OLIMEX/DIY-LAPTOP/doc/web/hw_in-the-box.md

# What do you get in the package?

With your DIY kit, you will receive:

Description                          | Images
:-----------------------------------:|:-----------------------------------:
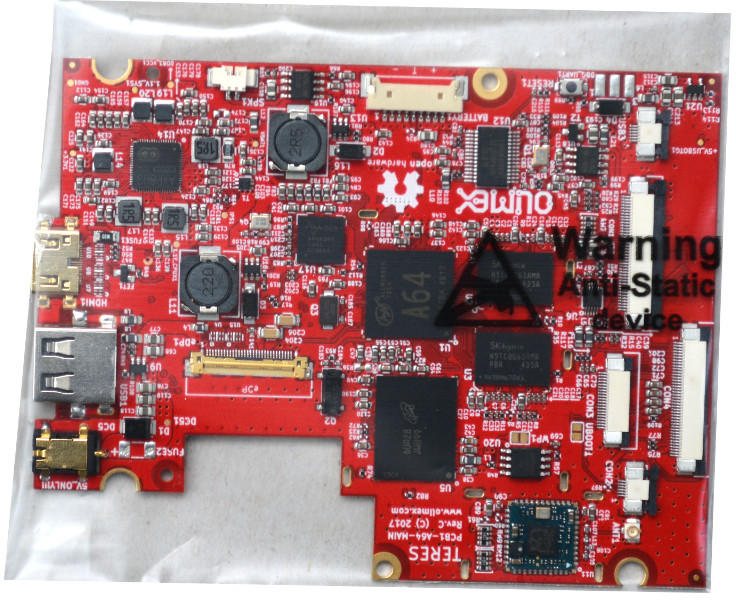
[picture p7: doc/images/TERES-I/hardware/001.jpg]
PCB1-A64-MAIN
| PCB1 (PCB1-A64-MAIN) – main PCB with A64 processor, 2GB RAM, 16GB eMMC. It is in an ESD protective bag. Please handle with proper anti-static precautions | 
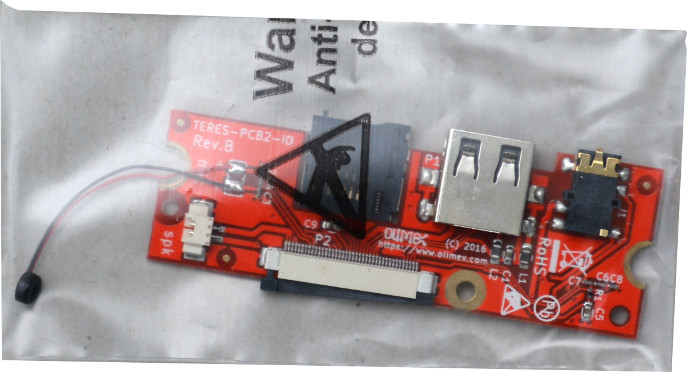
[picture p8: doc/images/TERES-I/hardware/002.jpg]
TERES-PCB2-IO
| PCB2 (TERES-PCB2-IO) – IO PCB with microphone, connectors for: speaker, USB, SD-card, headphones | 
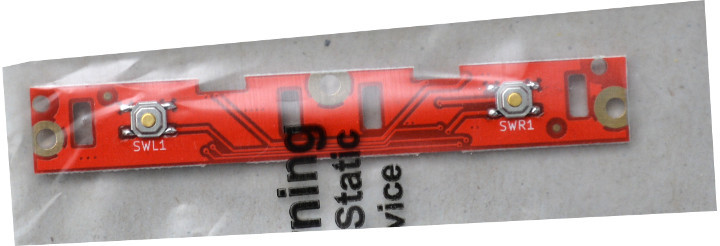
[picture p9: doc/images/TERES-I/hardware/003.jpg]
TERES-PCB3-TOUCH-BTN
| PCB3 (TERES-PCB3-TOUCH-BTN) – TOUCH two button PCB | 
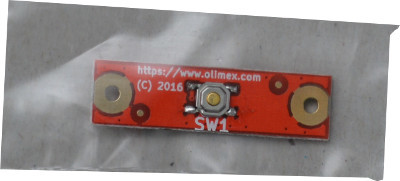
[picture p10: doc/images/TERES-I/hardware/004.jpg]
PCB4-PWR-BTN
| PCB4 – PWR PCB (PCB4-PWR-BTN) with button for power on/off | 
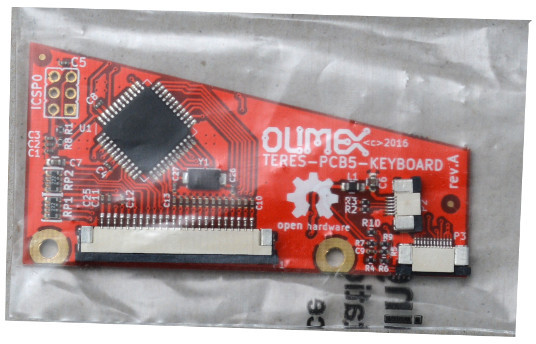
[picture p11: doc/images/TERES-I/hardware/005.jpg]
TERES-PCB5-KEYBOARD
| PCB5 (TERES-PCB5-KEYBOARD) – KEYBOARD PCB with controller of the keyboard and touchpad | 
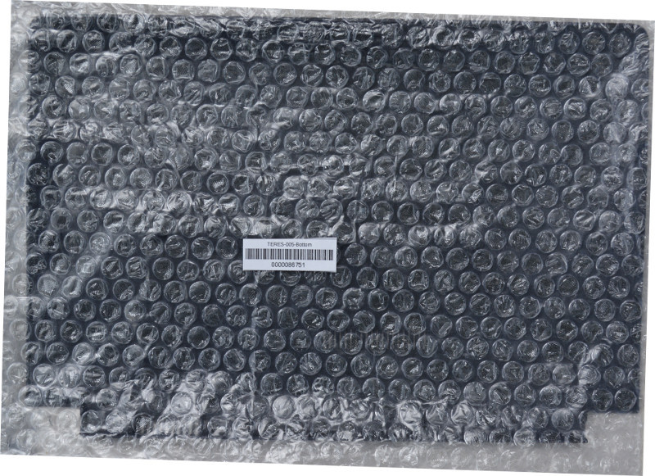
[picture p12: doc/images/TERES-I/hardware/006.jpg]
Bottom body 1
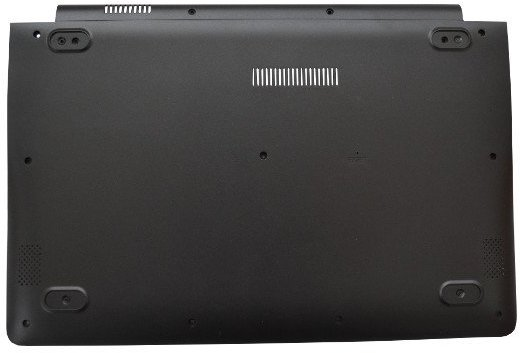
[picture p13: doc/images/TERES-I/hardware/007.jpg]
Bottom body 2
| Bottom body plastic part, packed in bubble wrap to protect from scratches |  
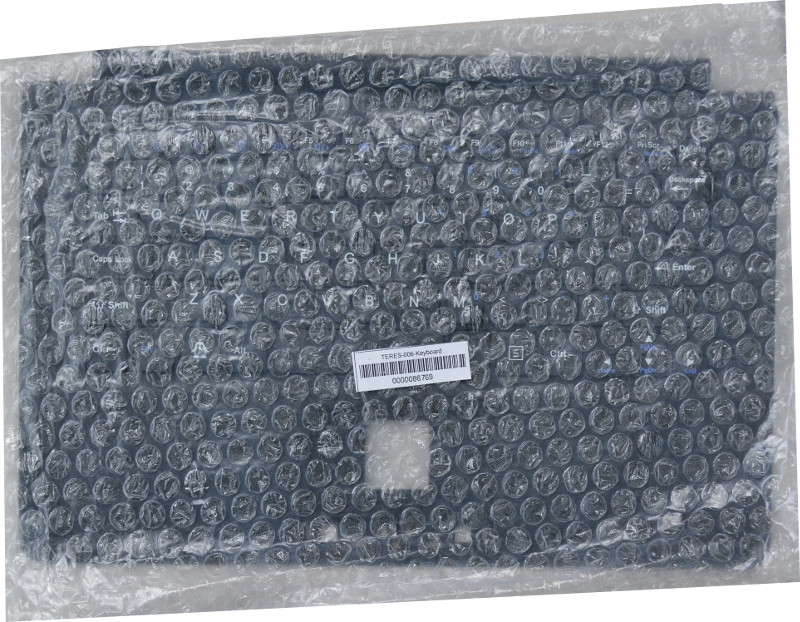
[picture p14: doc/images/TERES-I/hardware/008.jpg]
Keyboard body 1
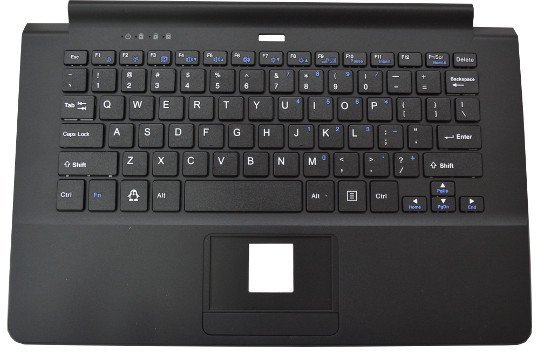
[picture p15: doc/images/TERES-I/hardware/009.jpg]
Keyboard body 2
| Keyboard body plastic assembly |  
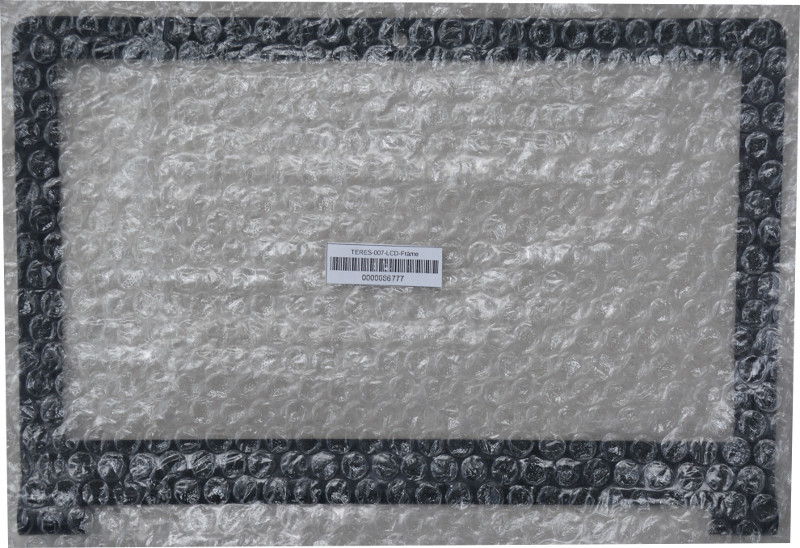
[picture p16: doc/images/TERES-I/hardware/010.jpg]
LCD frame 1
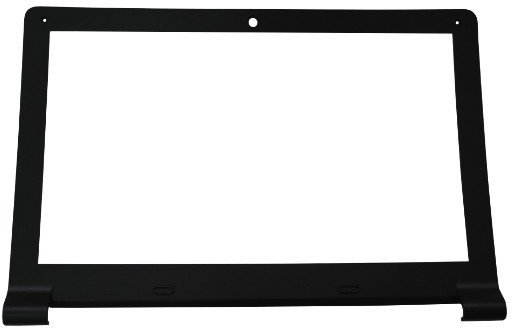
[picture p17: doc/images/TERES-I/hardware/011.jpg]
LCD frame 2
| LCD plastic frame |  
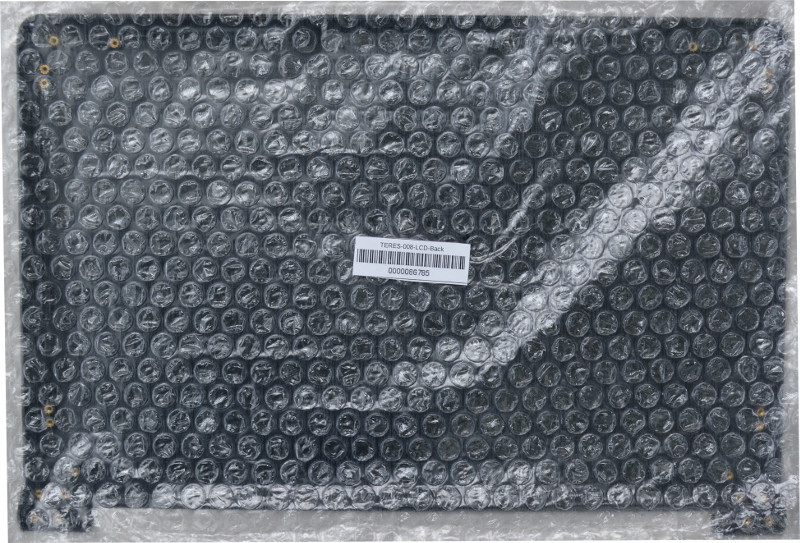
[picture p18: doc/images/TERES-I/hardware/012.jpg]
LCD body 1
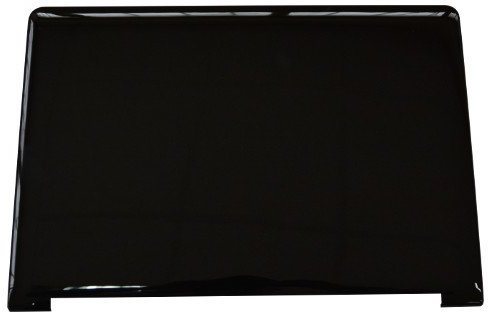
[picture p19: doc/images/TERES-I/hardware/013.jpg]
LCD body 2
| LCD back plastic body |  
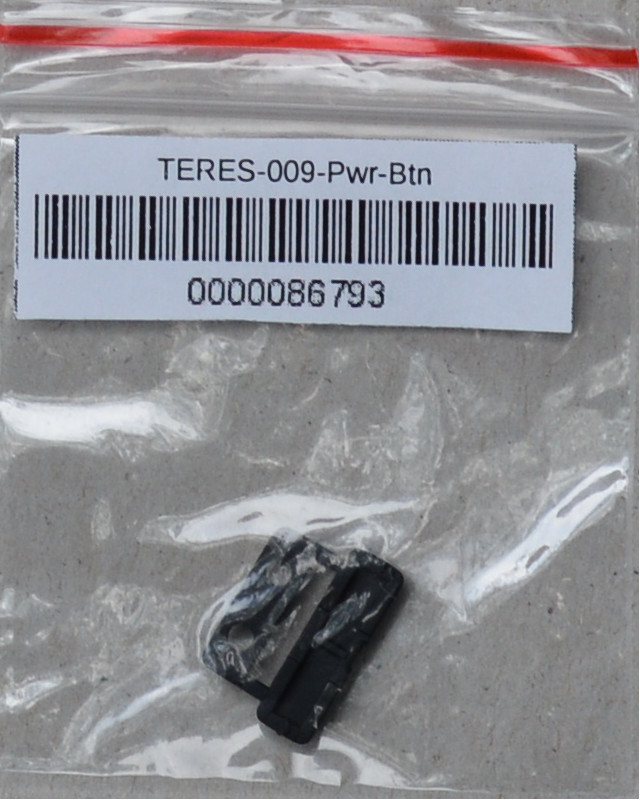
[picture p20: doc/images/TERES-I/hardware/014.jpg]
Power button 1
| Plastic power button |  Power button 2
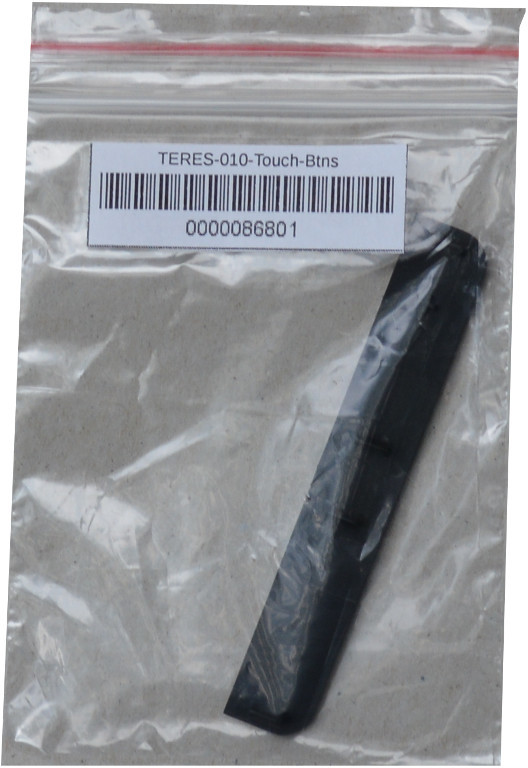
[picture p21: doc/images/TERES-I/hardware/016.jpg]
Touch button 1
| Plastic touch buttons |  Touch button 2
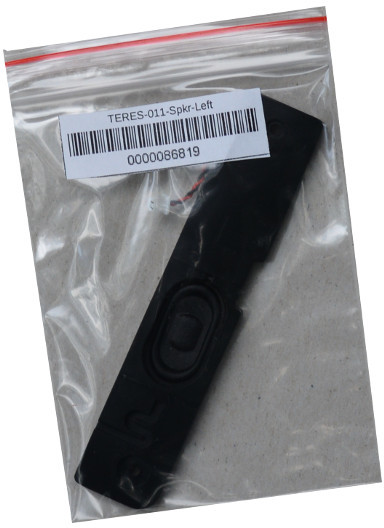
[picture p22: doc/images/TERES-I/hardware/018.jpg]
Left speaker 1
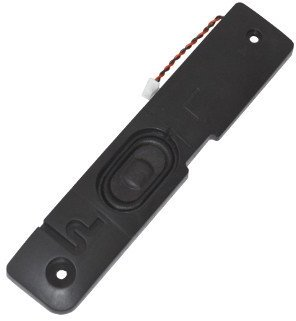
[picture p23: doc/images/TERES-I/hardware/019.jpg]
Left speaker 2
| Left speaker |  
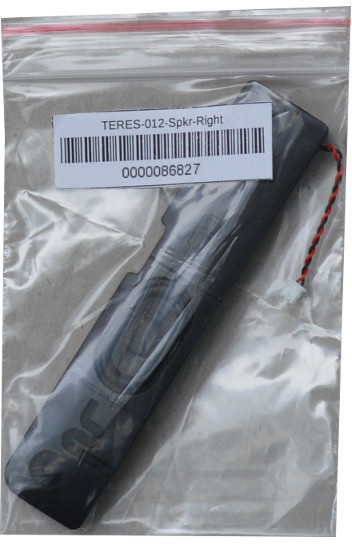
[picture p24: doc/images/TERES-I/hardware/020.jpg]
Right speaker 1
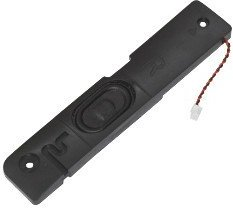
[picture p25: doc/images/TERES-I/hardware/021.jpg]
Right speaker 2
| Right speaker |  
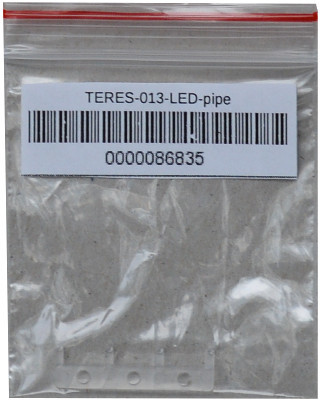
[picture p26: doc/images/TERES-I/hardware/022.jpg]
LED Pipe 1
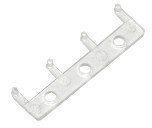
[picture p27: doc/images/TERES-I/hardware/023.jpg]
LED Pipe 2
| Transparent LED pipe |  
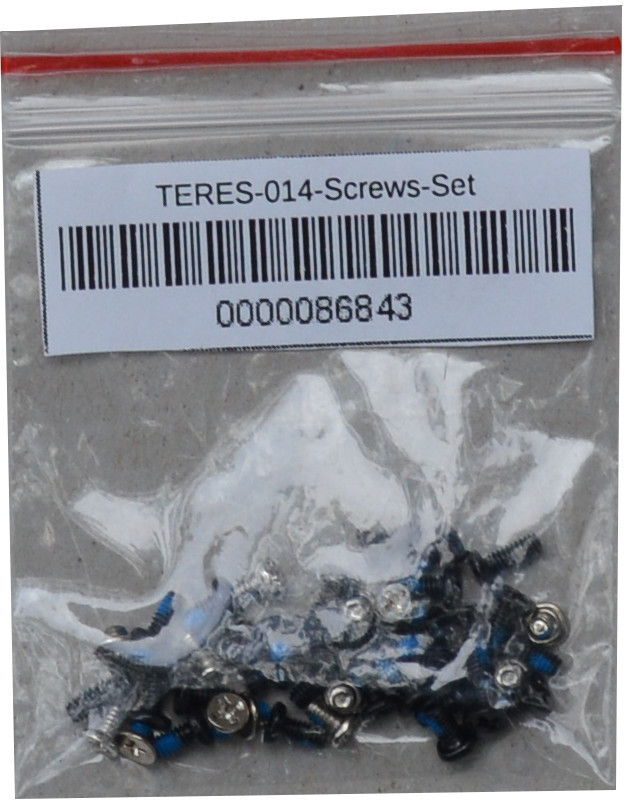
[picture p28: doc/images/TERES-I/hardware/024.jpg]
Screws 1
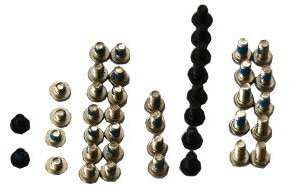
[picture p29: doc/images/TERES-I/hardware/025.jpg]
Screws 2
| Set of screws: M2x1.5 mm – 4 pcs; M2x3 mm – 9 pcs; M2x4 mm – 17 pcs; M2x5 mm – 12 pcs |  
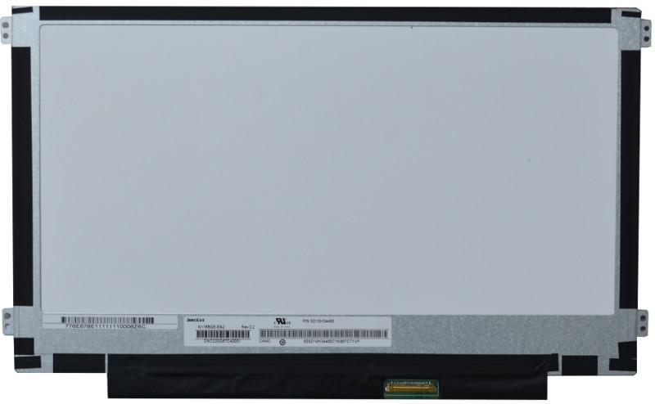
[picture p30: doc/images/TERES-I/hardware/026.jpg]
LCD 1
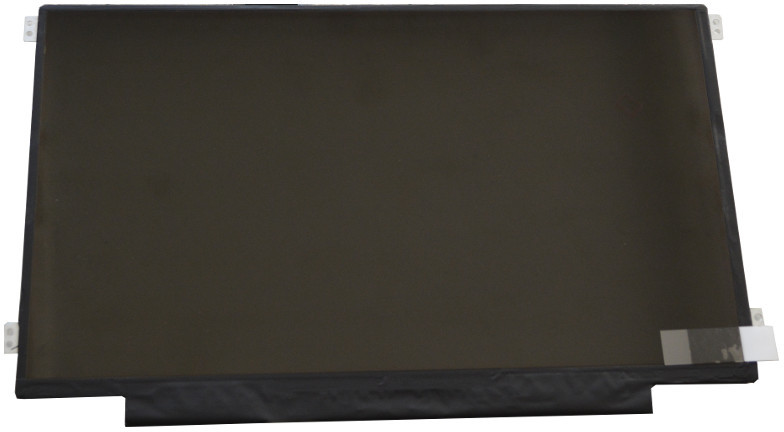
[picture p31: doc/images/TERES-I/hardware/027.jpg]
LCD 2
| [eDP](https://www.embedded.com/design/system-integration/4441940/eDP--A-better-embedded-display-ecosystem) 11.6" HD (1366x768) LCD. It has protective foil on top. [Datasheet](../datasheets/TERES-015-LCD11.6/N116BGE-EA2.pdf) |  
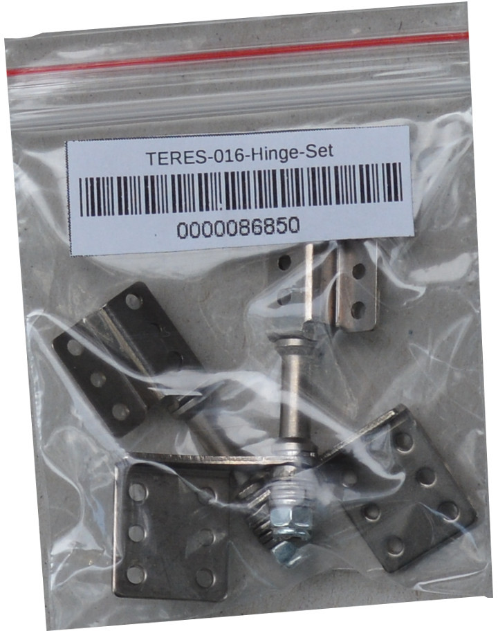
[picture p32: doc/images/TERES-I/hardware/028.jpg]
Hinges 1
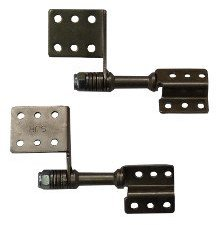
[picture p33: doc/images/TERES-I/hardware/029.jpg]
Hinges 2
| Left and right hinges |  
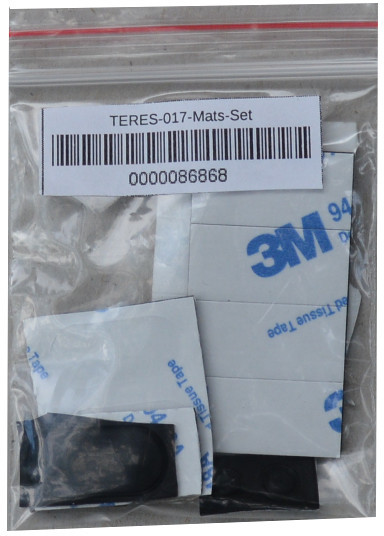
[picture p34: doc/images/TERES-I/hardware/030.jpg]
Mat 1
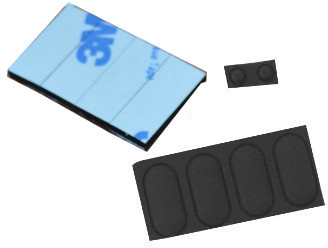
[picture p35: doc/images/TERES-I/hardware/031.jpg]
Mat 2
| Mat set. There are four rubber pads for the bottom of the laptop, two circular pads for LCD frame screws cover and four self adhesive mats for holding the battery. |  
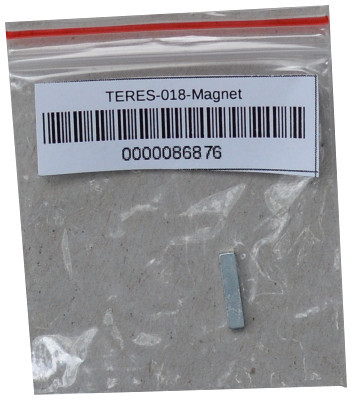
[picture p36: doc/images/TERES-I/hardware/032.jpg]
Magnet 1
| Magnet for the lid close sensor |  Magnet 2
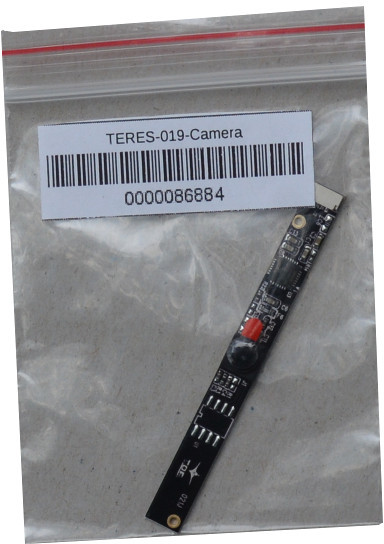
[picture p37: doc/images/TERES-I/hardware/034.jpg]
Camera 1
| Camera [[Datasheet](../../../HARDWARE/A64-TERES/TERES-019-Camera/N03A61B36DL32.pdf)] |  Camera 2
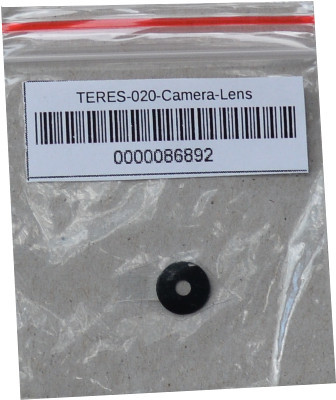
[picture p38: doc/images/TERES-I/hardware/036.jpg]
Camera lens 1
| Camera lens |  Camera lens 2
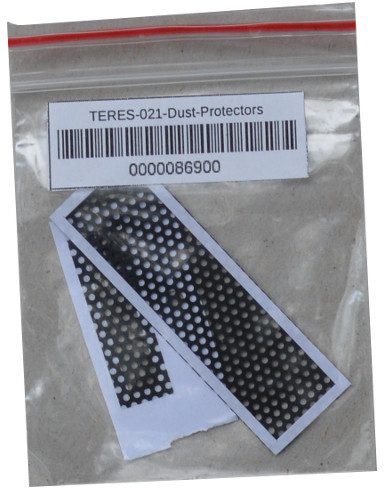
[picture p39: doc/images/TERES-I/hardware/038.jpg]
Dust protectors 1
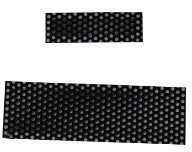
[picture p40: doc/images/TERES-I/hardware/039.jpg]
Dust protectors 2
| Two dust protectors – big and small |  
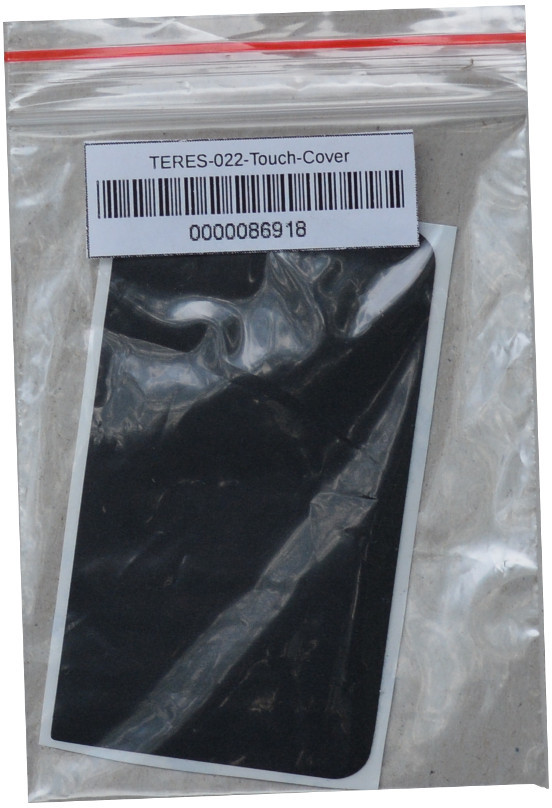
[picture p41: doc/images/TERES-I/hardware/040.jpg]
Touchpad cover 1
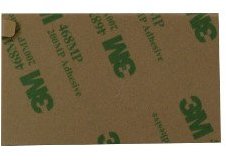
[picture p42: doc/images/TERES-I/hardware/042.jpg]
Touchpad cover 3
| Touchpad cover |  Touchpad cover 2 
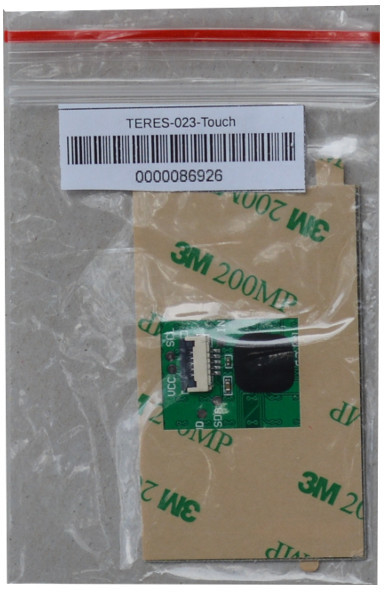
[picture p43: doc/images/TERES-I/hardware/043.jpg]
Touchpad
| Touchpad | 
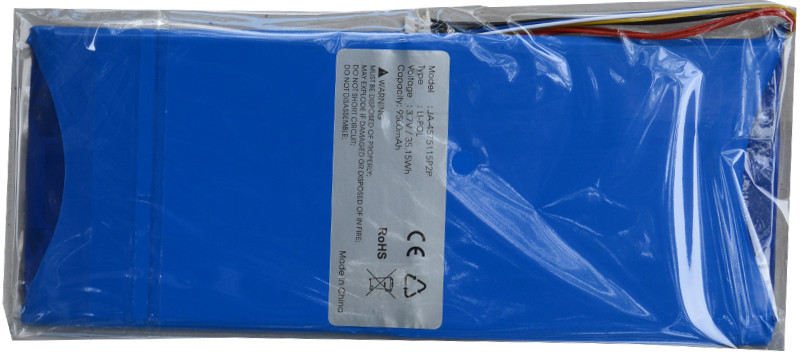
[picture p44: doc/images/TERES-I/hardware/044.jpg]
Battery
| LiPo battery 9500 mAh [[Datasheet](../../datasheets/LiPo-Battery/JA426992P2P-Spec-Data-Sheet-3.7V-7000mAh--161201.pdf)] | 
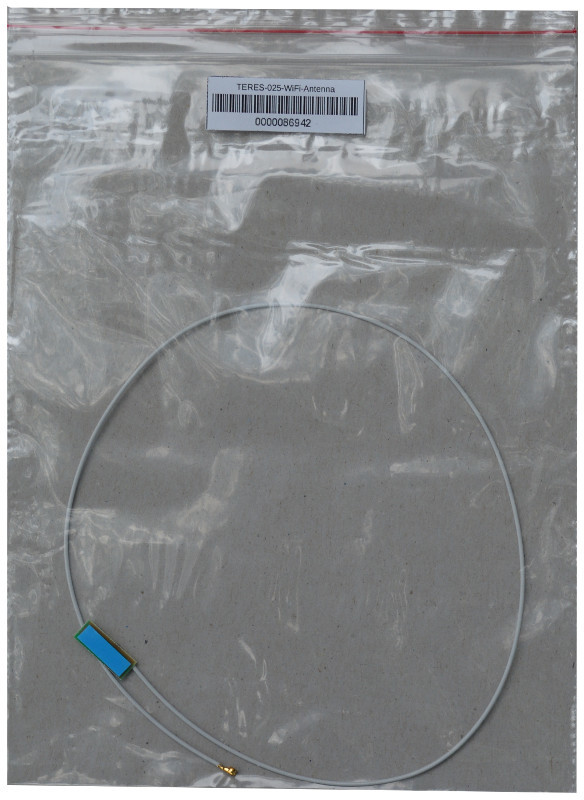
[picture p45: doc/images/TERES-I/hardware/045.jpg]
WiFi/Bluetooth 1
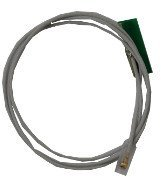
[picture p46: doc/images/TERES-I/hardware/046.jpg]
WiFi/Bluetooth 2
| WiFi/Bluetooth antenna |  
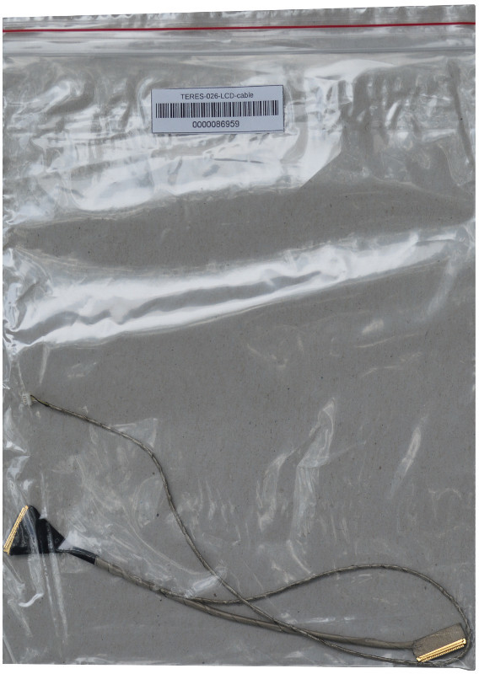
[picture p47: doc/images/TERES-I/hardware/047.jpg]
LCD/camera cable 1
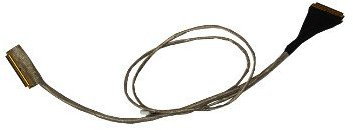
[picture p48: doc/images/TERES-I/hardware/048.jpg]
LCD/camera cable 2
| LCD/camera cable |  
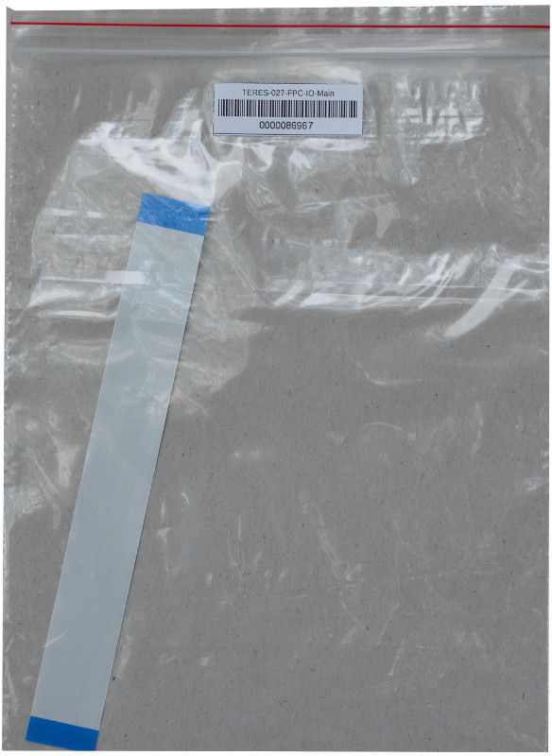
[picture p49: doc/images/TERES-I/hardware/049.jpg]
Main-IO cable 1
| Flat cable Main-IO |  Main-IO cable 2
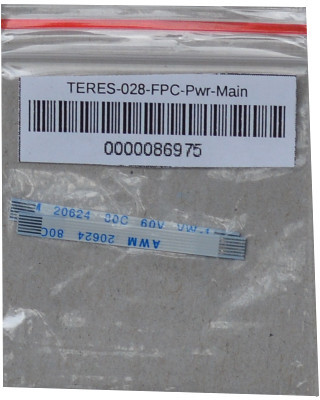
[picture p50: doc/images/TERES-I/hardware/051.jpg]
Flat cables 1
| Flat cable Power-Main, Flat cable Main-Keyboard |  Flat cables 2
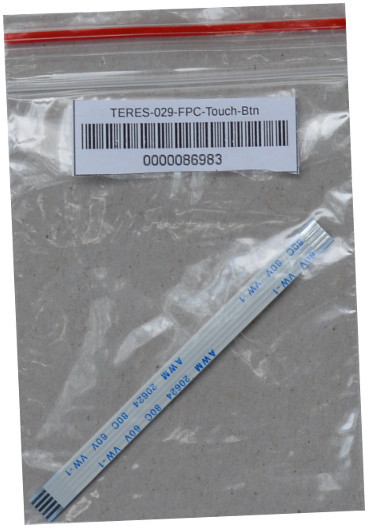
[picture p51: doc/images/TERES-I/hardware/053.jpg]
Touchpad-TouchButtons 1
| Flat cable Touchpad-TouchButtons |  Touchpad-TouchButtons 2
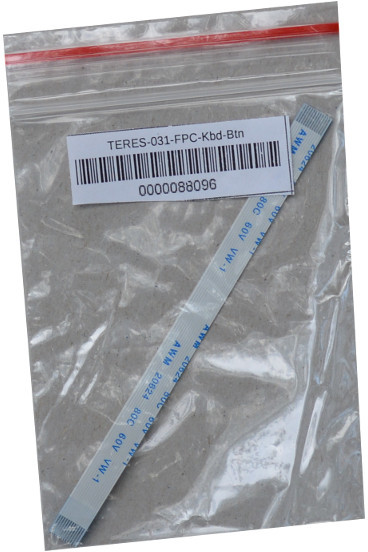
[picture p52: doc/images/TERES-I/hardware/055.jpg]
Keyboard-TouchButtons 1
| Flat cable Keyboard-TouchButtons |  Keyboard-TouchButtons 2
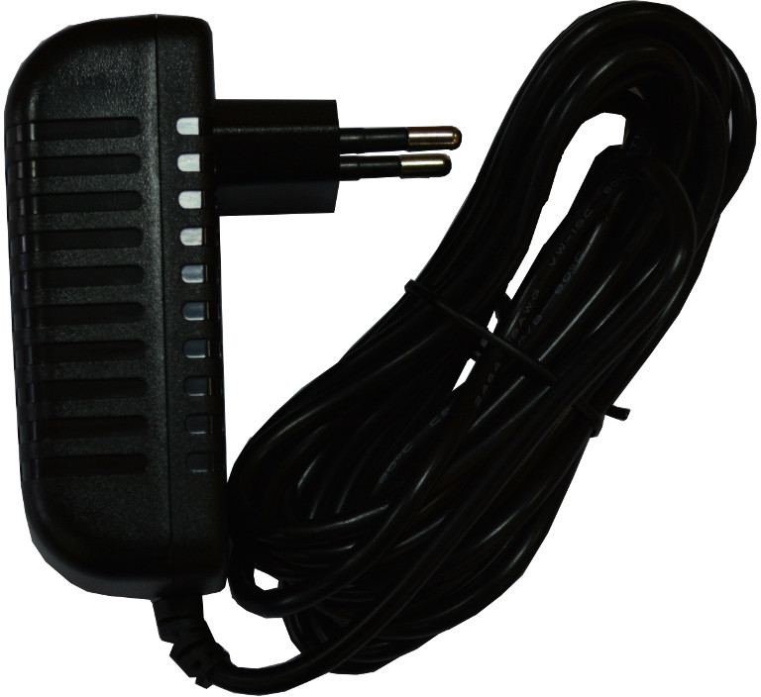
[picture p53: doc/images/TERES-I/hardware/057.jpg]
Power adapter 1
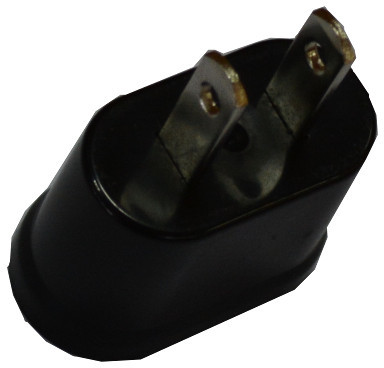
[picture p54: doc/images/TERES-I/hardware/058.jpg]
Power adapter 2
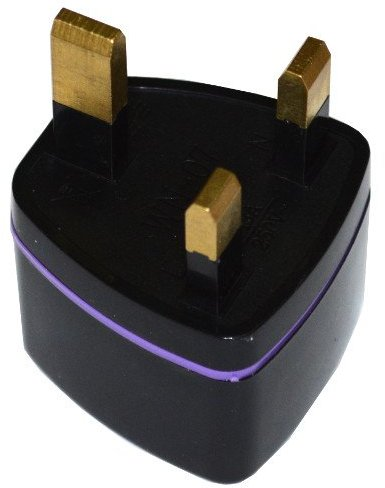
[picture p55: doc/images/TERES-I/hardware/059.jpg]
Power adapter 3
| Power adapter EU Style 5V 3A with 3 meter cable and LED status GREEN/RED indicator with UK and US plug adapters |
