OLIMEX/DIY-LAPTOP/index.rst

TERES-I User Manual
===================

.. toctree::
   :glob:
   :maxdepth: 2
   :caption: Overview

   doc/manuals/web/intro_what-is-teres-i
   doc/manuals/web/intro_name-origin
   doc/manuals/web/intro_what-is-unique
   doc/manuals/web/intro_importance-of-open-source
   doc/manuals/web/intro_sources

.. toctree::
   :glob:
   :maxdepth: 2
   :caption: Hardware

   doc/manuals/web/hw_intro
   doc/manuals/web/hw_in-the-box

.. toctree::
   :glob:
   :maxdepth: 2
   :caption: Assembling the TERES-I

   doc/manuals/web/hw_assembly

.. toctree::
   :glob:
   :maxdepth: 2
   :caption: Software

   doc/manuals/web/sw_fresh-os
   doc/manuals/web/sw_updating-os

.. toctree::
   :glob:
   :maxdepth: 2
   :caption: Resources

   doc/manuals/web/res_faq
   doc/manuals/web/res_troubleshooting
   doc/manuals/web/res_next-steps
   doc/manuals/web/res_community
