OLIMEX/DIY-LAPTOP/doc/web/res_community.md

# Community Links

<a href="https://www.github.com/OLIMEX" alt="GitHub" target="_blank" style="width: 50px; height: 50px" class="svg-link">
    <object data="../images/misc/icon-github.svg" type="image/svg+xml">
        
    </object>
</a>
<br>
<a href="https://twitter.com/Olimex" alt="Twitter" target="_blank" style="width: 50px; height: 50px" class="svg-link">
    <object data="../images/misc/icon-twitter.svg" type="image/svg+xml">
        
    </object>
</a>
<br>
<a href="https://olimex.wordpress.com" alt="Wordpress" target="_blank" style="width: 50px; height: 50px" class="svg-link">
    <object data="../images/misc/icon-wordpress.svg" type="image/svg+xml">
        
    </object>
</a>
<br>
<a href="https://www.facebook.com/OLINUXINO" alt="Facebook" target="_blank" style="width: 50px; height: 50px" class="svg-link">
    <object data="../images/misc/icon-facebook.svg" type="image/svg+xml">
        
    </object>
</a>
<br>
<a href="https://webchat.freenode.net/?channels=olimex" alt="IRC Web Chat" target="_blank" style="width: 50px; height: 50px" class="svg-link">
    <object data="../images/misc/icon-irc.jpg" type="image/svg+xml">
        
    </object>
</a>
