OLIMEX/DIY-LAPTOP/doc/images/TERES-I/TERES-A64-BLACK/laptop-3.jpg

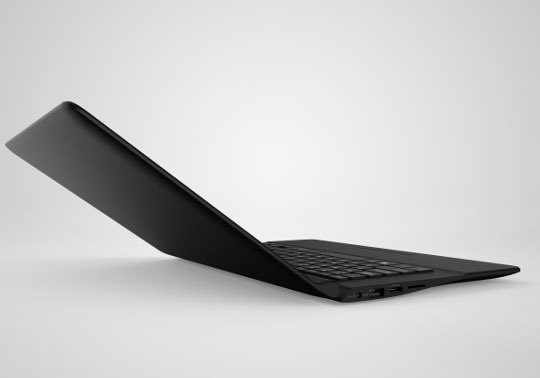
doc/images/TERES-I/TERES-A64-BLACK/laptop-3.jpg
