OLIMEX/DIY-LAPTOP/doc/images/TERES-I/TERES-A64-BLACK/laptop-9.jpg

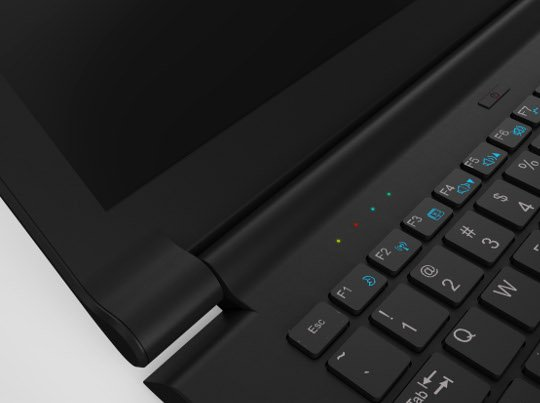
doc/images/TERES-I/TERES-A64-BLACK/laptop-9.jpg
