OLIMEX/DIY-LAPTOP/doc/images/TERES-I/TERES-A64-BLACK/laptop-16.jpg

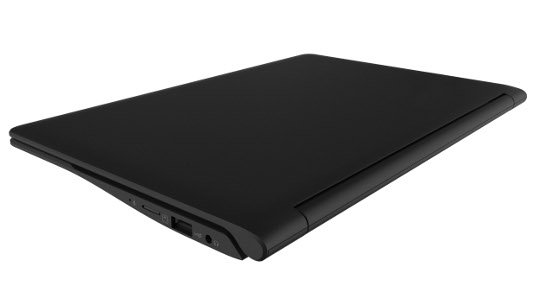
doc/images/TERES-I/TERES-A64-BLACK/laptop-16.jpg
