OLIMEX/DIY-LAPTOP/doc/images/TERES-I/TERES-A64-WHITE/laptop-1.jpg

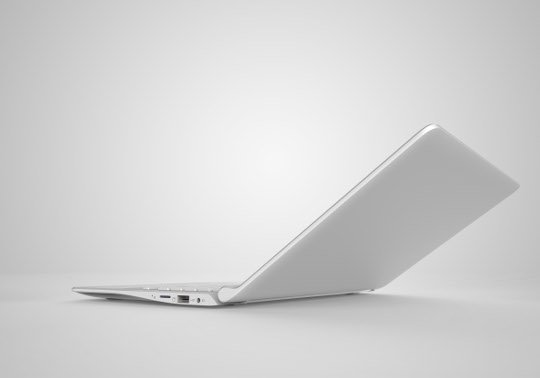
doc/images/TERES-I/TERES-A64-WHITE/laptop-1.jpg
