OLIMEX/DIY-LAPTOP/doc/images/TERES-I/TERES-A64-WHITE/laptop-5.jpg

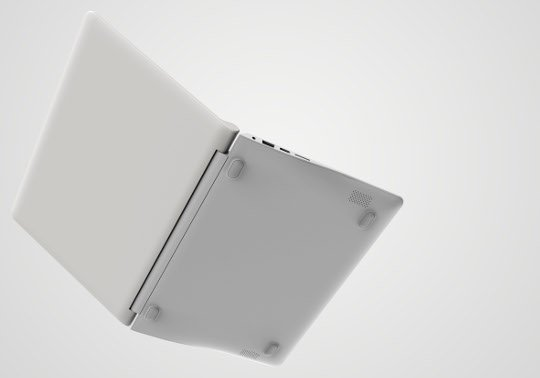
doc/images/TERES-I/TERES-A64-WHITE/laptop-5.jpg
