OLIMEX/DIY-LAPTOP/doc/images/TERES-I/TERES-A64-WHITE/laptop-7.jpg

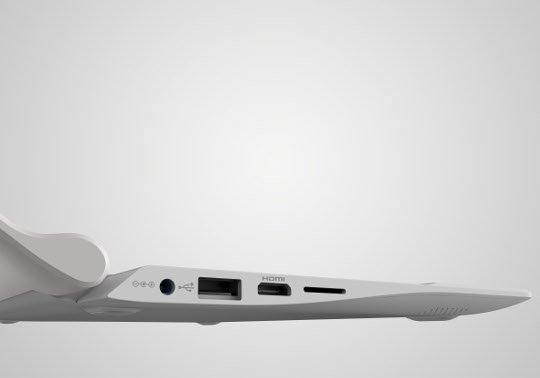
doc/images/TERES-I/TERES-A64-WHITE/laptop-7.jpg
