OLIMEX/DIY-LAPTOP/doc/images/TERES-I/TERES-A64-WHITE/laptop-15.jpg

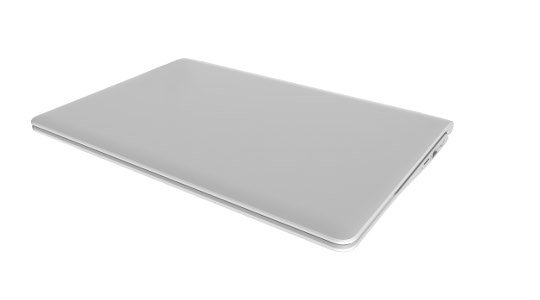
doc/images/TERES-I/TERES-A64-WHITE/laptop-15.jpg
