OLIMEX/DIY-LAPTOP/SOFTWARE/A64-TERES/blobs/bat/bat0.bmp

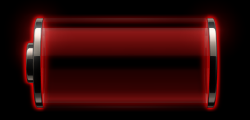
SOFTWARE/A64-TERES/blobs/bat/bat0.bmp
