OLIMEX/DIY-LAPTOP/SOFTWARE/A64-TERES/blobs/bat/bat1.bmp

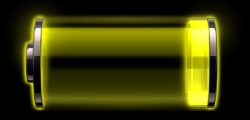
SOFTWARE/A64-TERES/blobs/bat/bat1.bmp
