OLIMEX/DIY-LAPTOP/SOFTWARE/A64-TERES/blobs/bat/bat2.bmp

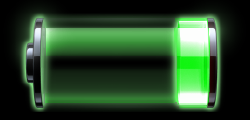
SOFTWARE/A64-TERES/blobs/bat/bat2.bmp
