OLIMEX/DIY-LAPTOP/SOFTWARE/A64-TERES/blobs/bat/bat3.bmp

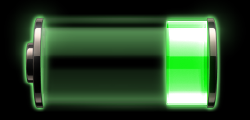
SOFTWARE/A64-TERES/blobs/bat/bat3.bmp
