OLIMEX/DIY-LAPTOP/SOFTWARE/A64-TERES/blobs/bat/bat4.bmp

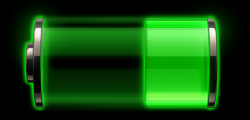
SOFTWARE/A64-TERES/blobs/bat/bat4.bmp
