OLIMEX/DIY-LAPTOP/SOFTWARE/A64-TERES/blobs/bat/bat5.bmp

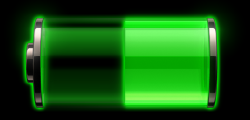
SOFTWARE/A64-TERES/blobs/bat/bat5.bmp
