OLIMEX/DIY-LAPTOP/SOFTWARE/A64-TERES/blobs/bat/bat6.bmp

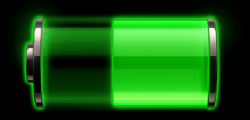
SOFTWARE/A64-TERES/blobs/bat/bat6.bmp
