OLIMEX/DIY-LAPTOP/SOFTWARE/A64-TERES/blobs/bat/bat7.bmp

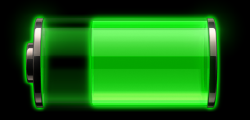
SOFTWARE/A64-TERES/blobs/bat/bat7.bmp
