OLIMEX/DIY-LAPTOP/SOFTWARE/A64-TERES/blobs/bat/bat8.bmp

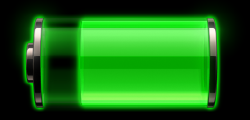
SOFTWARE/A64-TERES/blobs/bat/bat8.bmp
