OLIMEX/DIY-LAPTOP/SOFTWARE/A64-TERES/blobs/bat/bat9.bmp

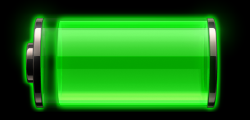
SOFTWARE/A64-TERES/blobs/bat/bat9.bmp
