OLIMEX/DIY-LAPTOP/SOFTWARE/A64-TERES/blobs/bat/bat10.bmp

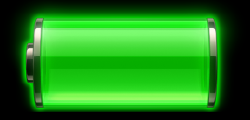
SOFTWARE/A64-TERES/blobs/bat/bat10.bmp
