OLIMEX/DIY-LAPTOP/SOFTWARE/A64-TERES/blobs/bat/battery.bmp

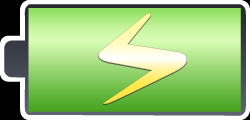
SOFTWARE/A64-TERES/blobs/bat/battery.bmp
