OLIMEX/DIY-LAPTOP/SOFTWARE/A64-TERES/blobs/bat/battery_charge.bmp

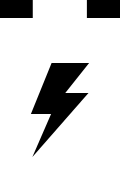
SOFTWARE/A64-TERES/blobs/bat/battery_charge.bmp
