OLIMEX/DIY-LAPTOP/SOFTWARE/A64-TERES/blobs/bat/bempty.bmp

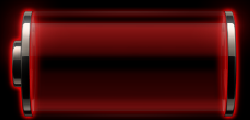
SOFTWARE/A64-TERES/blobs/bat/bempty.bmp
