OLIMEX/DIY-LAPTOP/SOFTWARE/A64-TERES/blobs/bat/low_pwr.bmp

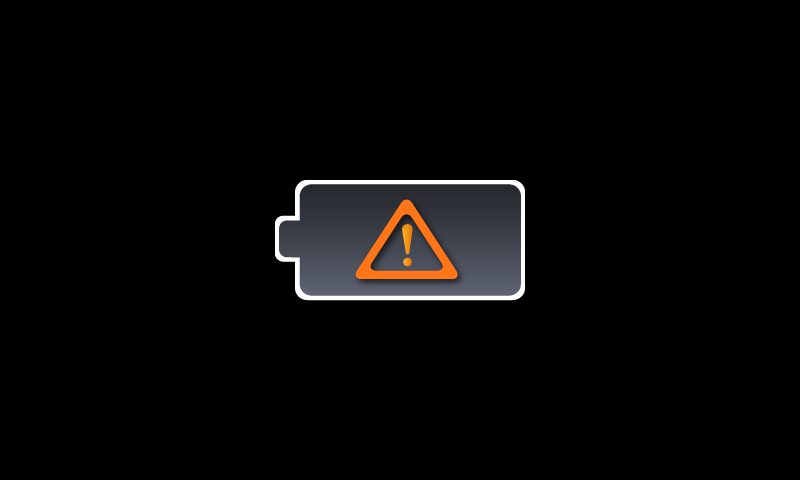
SOFTWARE/A64-TERES/blobs/bat/low_pwr.bmp
