OLIMEX/DIY-LAPTOP/HARDWARE/A64-TERES/TERES-PCB5-KEYBOARD/TERES-PCB5-KEYBOARD_Rev.A.ods

Designation | Quantity | Designator | Package
16.000MHz/SMD5x3.2/12pF | 1 | Y1 | Q5x3.25
ATMEGA16U4-A | 1 | U1 | TQFP44
FLEXCON-0.5-6 | 1 | P2 | FLEXCON-0.5-6
FLEXCON-0.5-12 | 1 | P3 | FLEXCON-0.5-12
FLEX-CONN-KBD-TERES-24x1 | 1 | P1 | FLEX-CONN-KBD-TERES-24x1
1uF | 1 | C1 | C0402
100nF | 6 | C2,C3,C4,C5,C8,C9 | C0402
1uF | 2 | C6,C7 | C_0603_5MIL_DWS
1nF | 16 | C10,C11,C12,C13,C14,C15,C16,C17,C18,C19,C20,C21,C22,C23,C24,C25 | C0402
20pF | 2 | C26,C27 | C0402
d.n.p.(HR2x3) | 1 | ICSP0 | HN2x3
FB0805 | 1 | L1 | L_0805_5MIL_DWS
d.n.p.(10K) | 1 | R1 | R_0402_5MIL_DWS
22R | 3 | R2,R3,R8 | R_0402_5MIL_DWS
10K | 6 | R4,R5,R6,R7,R9,R10 | R_0402_5MIL_DWS
4x1.5K_RA1206 | 2 | RP1,RP2 | R_MATRIX_4_KICAD
