OLIMEX/DIY-LAPTOP/SOFTWARE/A64-TERES/linux-a64/drivers/pinctrl/sunxi/pinctrl-sun8iw11p1.c

/*
 * Allwinner SoCs(sun8iw11p1) pinctrl driver.
 *
 * Copyright (C) 2014 Jackie Hwang
 *
 * Jackie Hwang <huangshr@allwinnertech.com>
 *
 * Copyright (C) 2014 Chen-Yu Tsai
 *
 * Chen-Yu Tsai <wens@csie.org>
 *
 * Copyright (C) 2014 Maxime Ripard
 *
 * Maxime Ripard <maxime.ripard@free-electrons.com>
 *
 * This file is licensed under the terms of the GNU General Public
 * License version 2.  This program is licensed "as is" without any
 * warranty of any kind, whether express or implied.
 */

#include <linux/module.h>
#include <linux/platform_device.h>
#include <linux/of.h>
#include <linux/of_device.h>
#include <linux/pinctrl/pinctrl.h>

#include "pinctrl-sunxi.h"
static const struct sunxi_desc_pin sun8iw11p1_pins[] = {
	SUNXI_PIN(SUNXI_PINCTRL_PIN(A, 0),
		  SUNXI_FUNCTION(0x0, "gpio_in"),
		  SUNXI_FUNCTION(0x1, "gpio_out"),
		  SUNXI_FUNCTION(0x2, "emac0"),		/* ERXD3 */
		  SUNXI_FUNCTION(0x3, "spi1"),		/* CS0 */
		  SUNXI_FUNCTION(0x4, "uart2"),		/* RTS */
		  SUNXI_FUNCTION(0x5, "gmac0"),		/* GRXD3 */
		  SUNXI_FUNCTION(0x7, "io_disabled")),
	SUNXI_PIN(SUNXI_PINCTRL_PIN(A, 1),
		  SUNXI_FUNCTION(0x0, "gpio_in"),
		  SUNXI_FUNCTION(0x1, "gpio_out"),
		  SUNXI_FUNCTION(0x2, "emac0"),		/* ERXD2 */
		  SUNXI_FUNCTION(0x3, "spi1"),		/* CLK */
		  SUNXI_FUNCTION(0x4, "uart2"),		/* CTS */
		  SUNXI_FUNCTION(0x5, "gmac0"),		/* GRXD2 */
		  SUNXI_FUNCTION(0x7, "io_disabled")),
	SUNXI_PIN(SUNXI_PINCTRL_PIN(A, 2),
		  SUNXI_FUNCTION(0x0, "gpio_in"),
		  SUNXI_FUNCTION(0x1, "gpio_out"),
		  SUNXI_FUNCTION(0x2, "emac0"),		/* ERXD1 */
		  SUNXI_FUNCTION(0x3, "spi1"),		/* MOSI */
		  SUNXI_FUNCTION(0x4, "uart2"),		/* TX */
		  SUNXI_FUNCTION(0x5, "gmac0"),		/* GRXD1 */
		  SUNXI_FUNCTION(0x7, "io_disabled")),
	SUNXI_PIN(SUNXI_PINCTRL_PIN(A, 3),
		  SUNXI_FUNCTION(0x0, "gpio_in"),
		  SUNXI_FUNCTION(0x1, "gpio_out"),
		  SUNXI_FUNCTION(0x2, "emac0"),		/* ERXD0 */
		  SUNXI_FUNCTION(0x3, "spi1"),		/* MISO */
		  SUNXI_FUNCTION(0x4, "uart2"),		/* RX */
		  SUNXI_FUNCTION(0x5, "gmac0"),		/* GRXD0 */
		  SUNXI_FUNCTION(0x7, "io_disabled")),
	SUNXI_PIN(SUNXI_PINCTRL_PIN(A, 4),
		  SUNXI_FUNCTION(0x0, "gpio_in"),
		  SUNXI_FUNCTION(0x1, "gpio_out"),
		  SUNXI_FUNCTION(0x2, "emac0"),		/* ETXD3 */
		  SUNXI_FUNCTION(0x3, "spi1"),		/* CS1 */
		  SUNXI_FUNCTION(0x5, "gmac0"),		/* GTXD3 */
		  SUNXI_FUNCTION(0x7, "io_disabled")),
	SUNXI_PIN(SUNXI_PINCTRL_PIN(A, 5),
		  SUNXI_FUNCTION(0x0, "gpio_in"),
		  SUNXI_FUNCTION(0x1, "gpio_out"),
		  SUNXI_FUNCTION(0x2, "emac0"),		/* ETXD2 */
		  SUNXI_FUNCTION(0x3, "spi3"),		/* CS0 */
		  SUNXI_FUNCTION(0x5, "gmac0"),		/* GTXD2 */
		  SUNXI_FUNCTION(0x7, "io_disabled")),
	SUNXI_PIN(SUNXI_PINCTRL_PIN(A, 6),
		  SUNXI_FUNCTION(0x0, "gpio_in"),
		  SUNXI_FUNCTION(0x1, "gpio_out"),
		  SUNXI_FUNCTION(0x2, "emac0"),		/* ETXD1 */
		  SUNXI_FUNCTION(0x3, "spi3"),		/* CLK */
		  SUNXI_FUNCTION(0x5, "gmac0"),		/* GTXD1 */
		  SUNXI_FUNCTION(0x7, "io_disabled")),
	SUNXI_PIN(SUNXI_PINCTRL_PIN(A, 7),
		  SUNXI_FUNCTION(0x0, "gpio_in"),
		  SUNXI_FUNCTION(0x1, "gpio_out"),
		  SUNXI_FUNCTION(0x2, "emac0"),		/* ETXD0 */
		  SUNXI_FUNCTION(0x3, "spi3"),		/* MOSI */
		  SUNXI_FUNCTION(0x5, "gmac0"),		/* GTXD0 */
		  SUNXI_FUNCTION(0x7, "io_disabled")),
	SUNXI_PIN(SUNXI_PINCTRL_PIN(A, 8),
		  SUNXI_FUNCTION(0x0, "gpio_in"),
		  SUNXI_FUNCTION(0x1, "gpio_out"),
		  SUNXI_FUNCTION(0x2, "emac0"),		/* ERXCK */
		  SUNXI_FUNCTION(0x3, "spi3"),		/* MISO */
		  SUNXI_FUNCTION(0x5, "gmac0"),		/* GRXCK */
		  SUNXI_FUNCTION(0x7, "io_disabled")),
	SUNXI_PIN(SUNXI_PINCTRL_PIN(A, 9),
		  SUNXI_FUNCTION(0x0, "gpio_in"),
		  SUNXI_FUNCTION(0x1, "gpio_out"),
		  SUNXI_FUNCTION(0x2, "emac0"),		/* ERXERR */
		  SUNXI_FUNCTION(0x3, "spi3"),		/* CS1 */
		  SUNXI_FUNCTION(0x5, "gmac0"),		/* GNULL / ERXERR */
		  SUNXI_FUNCTION(0x6, "i2s1"),		/* MCLK */
		  SUNXI_FUNCTION(0x7, "io_disabled")),
	SUNXI_PIN(SUNXI_PINCTRL_PIN(A, 10),
		  SUNXI_FUNCTION(0x0, "gpio_in"),
		  SUNXI_FUNCTION(0x1, "gpio_out"),
		  SUNXI_FUNCTION(0x2, "emac0"),		/* ERXDV */
		  SUNXI_FUNCTION(0x4, "uart1"),		/* TX */
		  SUNXI_FUNCTION(0x5, "gmac0"),		/* GRXCTL / ERXDV */
		  SUNXI_FUNCTION(0x7, "io_disabled")),
	SUNXI_PIN(SUNXI_PINCTRL_PIN(A, 11),
		  SUNXI_FUNCTION(0x0, "gpio_in"),
		  SUNXI_FUNCTION(0x1, "gpio_out"),
		  SUNXI_FUNCTION(0x2, "emac0"),		/* EMDC */
		  SUNXI_FUNCTION(0x4, "uart1"),		/* RX */
		  SUNXI_FUNCTION(0x5, "gmac0"),		/* GMDC */
		  SUNXI_FUNCTION(0x7, "io_disabled")),
	SUNXI_PIN(SUNXI_PINCTRL_PIN(A, 12),
		  SUNXI_FUNCTION(0x0, "gpio_in"),
		  SUNXI_FUNCTION(0x1, "gpio_out"),
		  SUNXI_FUNCTION(0x2, "emac0"),		/* EMDIO */
		  SUNXI_FUNCTION(0x3, "uart6"),		/* TX */
		  SUNXI_FUNCTION(0x4, "uart1"),		/* RTS */
		  SUNXI_FUNCTION(0x5, "gmac0"),		/* GMDIO */
		  SUNXI_FUNCTION(0x7, "io_disabled")),
	SUNXI_PIN(SUNXI_PINCTRL_PIN(A, 13),
		  SUNXI_FUNCTION(0x0, "gpio_in"),
		  SUNXI_FUNCTION(0x1, "gpio_out"),
		  SUNXI_FUNCTION(0x2, "emac0"),		/* ETXEN */
		  SUNXI_FUNCTION(0x3, "uart6"),		/* RX */
		  SUNXI_FUNCTION(0x4, "uart1"),		/* CTS */
		  SUNXI_FUNCTION(0x5, "gmac0"),		/* GTXCTL / ETXEN */
		  SUNXI_FUNCTION(0x7, "io_disabled")),
	SUNXI_PIN(SUNXI_PINCTRL_PIN(A, 14),
		  SUNXI_FUNCTION(0x0, "gpio_in"),
		  SUNXI_FUNCTION(0x1, "gpio_out"),
		  SUNXI_FUNCTION(0x2, "emac0"),		/* ETXCK */
		  SUNXI_FUNCTION(0x3, "uart7"),		/* TX */
		  SUNXI_FUNCTION(0x4, "uart1"),		/* DTR */
		  SUNXI_FUNCTION(0x5, "gmac0"),		/* GNULL / ETXCK */
		  SUNXI_FUNCTION(0x6, "i2s1"),		/* BCLK */
		  SUNXI_FUNCTION(0x7, "io_disabled")),
	SUNXI_PIN(SUNXI_PINCTRL_PIN(A, 15),
		  SUNXI_FUNCTION(0x0, "gpio_in"),
		  SUNXI_FUNCTION(0x1, "gpio_out"),
		  SUNXI_FUNCTION(0x2, "emac0"),		/* ECRS */
		  SUNXI_FUNCTION(0x3, "uart7"),		/* RX */
		  SUNXI_FUNCTION(0x4, "uart1"),		/* DSR */
		  SUNXI_FUNCTION(0x5, "gmac0"),		/* GTXCK / ECRS */
		  SUNXI_FUNCTION(0x6, "i2s1"),		/* LRCK */
		  SUNXI_FUNCTION(0x7, "io_disabled")),
	SUNXI_PIN(SUNXI_PINCTRL_PIN(A, 16),
		  SUNXI_FUNCTION(0x0, "gpio_in"),
		  SUNXI_FUNCTION(0x1, "gpio_out"),
		  SUNXI_FUNCTION(0x2, "emac0"),		/* ECOL */
		  SUNXI_FUNCTION(0x3, "can0"),		/* TX */
		  SUNXI_FUNCTION(0x4, "uart1"),		/* DCD */
		  SUNXI_FUNCTION(0x5, "gmac0"),		/* GCLKIN / ECOL */
		  SUNXI_FUNCTION(0x6, "i2s1"),		/* DO */
		  SUNXI_FUNCTION(0x7, "io_disabled")),
	SUNXI_PIN(SUNXI_PINCTRL_PIN(A, 17),
		  SUNXI_FUNCTION(0x0, "gpio_in"),
		  SUNXI_FUNCTION(0x1, "gpio_out"),
		  SUNXI_FUNCTION(0x2, "emac0"),		/* ETXERR */
		  SUNXI_FUNCTION(0x3, "can0"),		/* RX */
		  SUNXI_FUNCTION(0x4, "uart1"),		/* RING */
		  SUNXI_FUNCTION(0x5, "gmac0"),		/* GNULL / ETXERR */
		  SUNXI_FUNCTION(0x6, "i2s1"),		/* DI */
		  SUNXI_FUNCTION(0x7, "io_disabled")),

	/* Hole */
	SUNXI_PIN(SUNXI_PINCTRL_PIN(B, 0),
		  SUNXI_FUNCTION(0x0, "gpio_in"),
		  SUNXI_FUNCTION(0x1, "gpio_out"),
		  SUNXI_FUNCTION(0x2, "twi0"),		/* SCK */
		  SUNXI_FUNCTION(0x7, "io_disabled")),
	SUNXI_PIN(SUNXI_PINCTRL_PIN(B, 1),
		  SUNXI_FUNCTION(0x0, "gpio_in"),
		  SUNXI_FUNCTION(0x1, "gpio_out"),
		  SUNXI_FUNCTION(0x2, "twi0"),		/* SDA */
		  SUNXI_FUNCTION(0x7, "io_disabled")),
	SUNXI_PIN(SUNXI_PINCTRL_PIN(B, 2),
		  SUNXI_FUNCTION(0x0, "gpio_in"),
		  SUNXI_FUNCTION(0x1, "gpio_out"),
		  SUNXI_FUNCTION(0x2, "pwm0"),		/* PWM0 */
		  SUNXI_FUNCTION(0x7, "io_disabled")),
	SUNXI_PIN(SUNXI_PINCTRL_PIN(B, 3),
		  SUNXI_FUNCTION(0x0, "gpio_in"),
		  SUNXI_FUNCTION(0x1, "gpio_out"),
		  SUNXI_FUNCTION(0x2, "ir0"),		/* TX */
		  SUNXI_FUNCTION(0x4, "spdif0"),	/* MCLK */
		  SUNXI_FUNCTION(0x6, "stanbywfi"),	/* STANBYWFI */
		  SUNXI_FUNCTION(0x7, "io_disabled")),
	SUNXI_PIN(SUNXI_PINCTRL_PIN(B, 4),
		  SUNXI_FUNCTION(0x0, "gpio_in"),
		  SUNXI_FUNCTION(0x1, "gpio_out"),
		  SUNXI_FUNCTION(0x2, "ir0"),		/* RX */
		  SUNXI_FUNCTION(0x7, "io_disabled")),
	SUNXI_PIN(SUNXI_PINCTRL_PIN(B, 5),
		  SUNXI_FUNCTION(0x0, "gpio_in"),
		  SUNXI_FUNCTION(0x1, "gpio_out"),
		  SUNXI_FUNCTION(0x2, "i2s0"),		/* MCLK */
		  SUNXI_FUNCTION(0x3, "ac97"),		/* MCLK */
		  SUNXI_FUNCTION(0x7, "io_disabled")),
	SUNXI_PIN(SUNXI_PINCTRL_PIN(B, 6),
		  SUNXI_FUNCTION(0x0, "gpio_in"),
		  SUNXI_FUNCTION(0x1, "gpio_out"),
		  SUNXI_FUNCTION(0x2, "i2s0"),		/* BCLK */
		  SUNXI_FUNCTION(0x3, "ac97"),		/* BCLK */
		  SUNXI_FUNCTION(0x7, "io_disabled")),
	SUNXI_PIN(SUNXI_PINCTRL_PIN(B, 7),
		  SUNXI_FUNCTION(0x0, "gpio_in"),
		  SUNXI_FUNCTION(0x1, "gpio_out"),
		  SUNXI_FUNCTION(0x2, "i2s0"),		/* LRCK */
		  SUNXI_FUNCTION(0x3, "ac97"),		/* SYNC */
		  SUNXI_FUNCTION(0x7, "io_disabled")),
	SUNXI_PIN(SUNXI_PINCTRL_PIN(B, 8),
		  SUNXI_FUNCTION(0x0, "gpio_in"),
		  SUNXI_FUNCTION(0x1, "gpio_out"),
		  SUNXI_FUNCTION(0x2, "i2s0"),		/* DO0 */
		  SUNXI_FUNCTION(0x3, "ac97"),		/* DO */
		  SUNXI_FUNCTION(0x7, "io_disabled")),
	SUNXI_PIN(SUNXI_PINCTRL_PIN(B, 9),
		  SUNXI_FUNCTION(0x0, "gpio_in"),
		  SUNXI_FUNCTION(0x1, "gpio_out"),
		  SUNXI_FUNCTION(0x2, "i2s0"),		/* DO1 */
		  SUNXI_FUNCTION(0x7, "io_disabled")),
	SUNXI_PIN(SUNXI_PINCTRL_PIN(B, 10),
		  SUNXI_FUNCTION(0x0, "gpio_in"),
		  SUNXI_FUNCTION(0x1, "gpio_out"),
		  SUNXI_FUNCTION(0x2, "i2s0"),		/* DO2 */
		  SUNXI_FUNCTION(0x7, "io_disabled")),
	SUNXI_PIN(SUNXI_PINCTRL_PIN(B, 11),
		  SUNXI_FUNCTION(0x0, "gpio_in"),
		  SUNXI_FUNCTION(0x1, "gpio_out"),
		  SUNXI_FUNCTION(0x2, "i2s0"),		/* DO3 */
		  SUNXI_FUNCTION(0x7, "io_disabled")),
	SUNXI_PIN(SUNXI_PINCTRL_PIN(B, 12),
		  SUNXI_FUNCTION(0x0, "gpio_in"),
		  SUNXI_FUNCTION(0x1, "gpio_out"),
		  SUNXI_FUNCTION(0x2, "i2s0"),		/* DI */
		  SUNXI_FUNCTION(0x3, "ac97"),		/* DI */
		  SUNXI_FUNCTION(0x4, "spdif0"),	/* DI */
		  SUNXI_FUNCTION(0x7, "io_disabled")),
	SUNXI_PIN(SUNXI_PINCTRL_PIN(B, 13),
		  SUNXI_FUNCTION(0x0, "gpio_in"),
		  SUNXI_FUNCTION(0x1, "gpio_out"),
		  SUNXI_FUNCTION(0x2, "spi2"),		/* CS1 */
		  SUNXI_FUNCTION(0x4, "spdif0"),	/* DO */
		  SUNXI_FUNCTION(0x7, "io_disabled")),
	SUNXI_PIN(SUNXI_PINCTRL_PIN(B, 14),
		  SUNXI_FUNCTION(0x0, "gpio_in"),
		  SUNXI_FUNCTION(0x1, "gpio_out"),
		  SUNXI_FUNCTION(0x2, "spi2"),		/* CS0 */
		  SUNXI_FUNCTION(0x3, "jtag0"),		/* MS0 */
		  SUNXI_FUNCTION(0x7, "io_disabled")),
	SUNXI_PIN(SUNXI_PINCTRL_PIN(B, 15),
		  SUNXI_FUNCTION(0x0, "gpio_in"),
		  SUNXI_FUNCTION(0x1, "gpio_out"),
		  SUNXI_FUNCTION(0x2, "spi2"),		/* CLK */
		  SUNXI_FUNCTION(0x3, "jtag0"),		/* CK0 */
		  SUNXI_FUNCTION(0x7, "io_disabled")),
	SUNXI_PIN(SUNXI_PINCTRL_PIN(B, 16),
		  SUNXI_FUNCTION(0x0, "gpio_in"),
		  SUNXI_FUNCTION(0x1, "gpio_out"),
		  SUNXI_FUNCTION(0x2, "spi2"),		/* MOSI */
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
		  SUNXI_FUNCTION(0x0, "gpio_in"),
		  SUNXI_FUNCTION(0x1, "gpio_out"),
		  SUNXI_FUNCTION(0x2, "ts0"),		/* D4 */
		  SUNXI_FUNCTION(0x3, "csi0"),		/* D4 */
		  SUNXI_FUNCTION(0x7, "io_disabled")),
	SUNXI_PIN(SUNXI_PINCTRL_PIN(E, 9),
		  SUNXI_FUNCTION(0x0, "gpio_in"),
		  SUNXI_FUNCTION(0x1, "gpio_out"),
		  SUNXI_FUNCTION(0x2, "ts0"),		/* D5 */
		  SUNXI_FUNCTION(0x3, "csi0"),		/* D5 */
		  SUNXI_FUNCTION(0x7, "io_disabled")),
	SUNXI_PIN(SUNXI_PINCTRL_PIN(E, 10),
		  SUNXI_FUNCTION(0x0, "gpio_in"),
		  SUNXI_FUNCTION(0x1, "gpio_out"),
		  SUNXI_FUNCTION(0x2, "ts0"),		/* D6 */
		  SUNXI_FUNCTION(0x3, "csi0"),		/* D6 */
		  SUNXI_FUNCTION(0x7, "io_disabled")),
	SUNXI_PIN(SUNXI_PINCTRL_PIN(E, 11),
		  SUNXI_FUNCTION(0x0, "gpio_in"),
		  SUNXI_FUNCTION(0x1, "gpio_out"),
		  SUNXI_FUNCTION(0x2, "ts0"),		/* D7 */
		  SUNXI_FUNCTION(0x3, "csi0"),		/* D7 */
		  SUNXI_FUNCTION(0x7, "io_disabled")),

	/* Hole */
	SUNXI_PIN(SUNXI_PINCTRL_PIN(F, 0),
		  SUNXI_FUNCTION(0x0, "gpio_in"),
		  SUNXI_FUNCTION(0x1, "gpio_out"),
		  SUNXI_FUNCTION(0x2, "sdc0"),		/* D1 */
		  SUNXI_FUNCTION(0x4, "jtag0"),		/* MSI */
		  SUNXI_FUNCTION(0x7, "io_disabled")),
	SUNXI_PIN(SUNXI_PINCTRL_PIN(F, 1),
		  SUNXI_FUNCTION(0x0, "gpio_in"),
		  SUNXI_FUNCTION(0x1, "gpio_out"),
		  SUNXI_FUNCTION(0x2, "sdc0"),		/* D0 */
		  SUNXI_FUNCTION(0x4, "jtag0"),		/* DI1 */
		  SUNXI_FUNCTION(0x7, "io_disabled")),
	SUNXI_PIN(SUNXI_PINCTRL_PIN(F, 2),
		  SUNXI_FUNCTION(0x0, "gpio_in"),
		  SUNXI_FUNCTION(0x1, "gpio_out"),
		  SUNXI_FUNCTION(0x2, "sdc0"),		/* CLK */
		  SUNXI_FUNCTION(0x4, "uart0"),		/* TX */
		  SUNXI_FUNCTION(0x7, "io_disabled")),
	SUNXI_PIN(SUNXI_PINCTRL_PIN(F, 3),
		  SUNXI_FUNCTION(0x0, "gpio_in"),
		  SUNXI_FUNCTION(0x1, "gpio_out"),
		  SUNXI_FUNCTION(0x2, "sdc0"),		/* CMD */
		  SUNXI_FUNCTION(0x4, "jtag0"),		/* DO1 */
		  SUNXI_FUNCTION(0x7, "io_disabled")),
	SUNXI_PIN(SUNXI_PINCTRL_PIN(F, 4),
		  SUNXI_FUNCTION(0x0, "gpio_in"),
		  SUNXI_FUNCTION(0x1, "gpio_out"),
		  SUNXI_FUNCTION(0x2, "sdc0"),		/* D3 */
		  SUNXI_FUNCTION(0x4, "uart0"),		/* RX */
		  SUNXI_FUNCTION(0x7, "io_disabled")),
	SUNXI_PIN(SUNXI_PINCTRL_PIN(F, 5),
		  SUNXI_FUNCTION(0x0, "gpio_in"),
		  SUNXI_FUNCTION(0x1, "gpio_out"),
		  SUNXI_FUNCTION(0x2, "sdc0"),		/* D2 */
		  SUNXI_FUNCTION(0x4, "jtag0"),		/* CK1 */
		  SUNXI_FUNCTION(0x7, "io_disabled")),

	/* Hole */
	SUNXI_PIN(SUNXI_PINCTRL_PIN(G, 0),
		  SUNXI_FUNCTION(0x0, "gpio_in"),
		  SUNXI_FUNCTION(0x1, "gpio_out"),
		  SUNXI_FUNCTION(0x2, "ts1"),		/* CLK */
		  SUNXI_FUNCTION(0x3, "csi1"),		/* PCLK */
		  SUNXI_FUNCTION(0x4, "sdc1"),		/* CMD */
		  SUNXI_FUNCTION(0x7, "io_disabled")),
	SUNXI_PIN(SUNXI_PINCTRL_PIN(G, 1),
		  SUNXI_FUNCTION(0x0, "gpio_in"),
		  SUNXI_FUNCTION(0x1, "gpio_out"),
		  SUNXI_FUNCTION(0x2, "ts1"),		/* ERR */
		  SUNXI_FUNCTION(0x3, "csi1"),		/* MLCK */
		  SUNXI_FUNCTION(0x4, "sdc1"),		/* CLK */
		  SUNXI_FUNCTION(0x7, "io_disabled")),
	SUNXI_PIN(SUNXI_PINCTRL_PIN(G, 2),
		  SUNXI_FUNCTION(0x0, "gpio_in"),
		  SUNXI_FUNCTION(0x1, "gpio_out"),
		  SUNXI_FUNCTION(0x2, "ts1"),		/* SYNC */
		  SUNXI_FUNCTION(0x3, "csi1"),		/* HSYNC */
		  SUNXI_FUNCTION(0x4, "sdc1"),		/* D0 */
		  SUNXI_FUNCTION(0x7, "io_disabled")),
	SUNXI_PIN(SUNXI_PINCTRL_PIN(G, 3),
		  SUNXI_FUNCTION(0x0, "gpio_in"),
		  SUNXI_FUNCTION(0x1, "gpio_out"),
		  SUNXI_FUNCTION(0x2, "ts1"),		/* DVLD */
		  SUNXI_FUNCTION(0x3, "csi1"),		/* VSYNC */
		  SUNXI_FUNCTION(0x4, "sdc1"),		/* D1 */
		  SUNXI_FUNCTION(0x7, "io_disabled")),
	SUNXI_PIN(SUNXI_PINCTRL_PIN(G, 4),
		  SUNXI_FUNCTION(0x0, "gpio_in"),
		  SUNXI_FUNCTION(0x1, "gpio_out"),
		  SUNXI_FUNCTION(0x2, "ts1"),		/* D0 */
		  SUNXI_FUNCTION(0x3, "csi1"),		/* D0 */
		  SUNXI_FUNCTION(0x4, "sdc1"),		/* D2 */
		  SUNXI_FUNCTION(0x5, "csi0"),		/* D8 */
		  SUNXI_FUNCTION(0x7, "io_disabled")),
	SUNXI_PIN(SUNXI_PINCTRL_PIN(G, 5),
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
		  SUNXI_FUNCTION(0x0, "gpio_in"),
		  SUNXI_FUNCTION(0x1, "gpio_out"),
		  SUNXI_FUNCTION(0x2, "lcd1"),		/* D15 */
		  SUNXI_FUNCTION(0x3, "emac0"),		/* ETXD2 */
		  SUNXI_FUNCTION(0x4, "kp0"),		/* IN5 */
		  SUNXI_FUNCTION(0x5, "sim0"),		/* VPPPP */
		  SUNXI_FUNCTION(0x7, "csi1"),		/* D15 */
		  SUNXI_FUNCTION_IRQ_BANK(0x6, 0, 15)),
	SUNXI_PIN(SUNXI_PINCTRL_PIN(H, 16),
		  SUNXI_FUNCTION(0x0, "gpio_in"),
		  SUNXI_FUNCTION(0x1, "gpio_out"),
		  SUNXI_FUNCTION(0x2, "lcd1"),		/* D16 */
		  SUNXI_FUNCTION(0x3, "emac0"),		/* ETXD1 */
		  SUNXI_FUNCTION(0x4, "kp0"),		/* IN6 */
		  SUNXI_FUNCTION(0x7, "csi1"),		/* D16 */
		  SUNXI_FUNCTION_IRQ_BANK(0x6, 0, 16)),
	SUNXI_PIN(SUNXI_PINCTRL_PIN(H, 17),
		  SUNXI_FUNCTION(0x0, "gpio_in"),
		  SUNXI_FUNCTION(0x1, "gpio_out"),
		  SUNXI_FUNCTION(0x2, "lcd1"),		/* D17 */
		  SUNXI_FUNCTION(0x3, "emac0"),		/* ETXD0 */
		  SUNXI_FUNCTION(0x4, "kp0"),		/* IN7 */
		  SUNXI_FUNCTION(0x5, "sim0"),		/* VCCEN */
		  SUNXI_FUNCTION(0x7, "csi1"),		/* D17 */
		  SUNXI_FUNCTION_IRQ_BANK(0x6, 0, 17)),
	SUNXI_PIN(SUNXI_PINCTRL_PIN(H, 18),
		  SUNXI_FUNCTION(0x0, "gpio_in"),
		  SUNXI_FUNCTION(0x1, "gpio_out"),
		  SUNXI_FUNCTION(0x2, "lcd1"),		/* D18 */
		  SUNXI_FUNCTION(0x3, "emac0"),		/* ERXCK */
		  SUNXI_FUNCTION(0x4, "kp0"),		/* OUT0 */
		  SUNXI_FUNCTION(0x5, "sim0"),		/* SLK */
		  SUNXI_FUNCTION(0x7, "csi1"),		/* D18 */
		  SUNXI_FUNCTION_IRQ_BANK(0x6, 0, 18)),
	SUNXI_PIN(SUNXI_PINCTRL_PIN(H, 19),
		  SUNXI_FUNCTION(0x0, "gpio_in"),
		  SUNXI_FUNCTION(0x1, "gpio_out"),
		  SUNXI_FUNCTION(0x2, "lcd1"),		/* D19 */
		  SUNXI_FUNCTION(0x3, "emac0"),		/* ERXERR */
		  SUNXI_FUNCTION(0x4, "kp0"),		/* OUT1 */
		  SUNXI_FUNCTION(0x5, "sim0"),		/* SDA */
		  SUNXI_FUNCTION(0x7, "csi1"),		/* D19 */
		  SUNXI_FUNCTION_IRQ_BANK(0x6, 0, 19)),
	SUNXI_PIN(SUNXI_PINCTRL_PIN(H, 20),
		  SUNXI_FUNCTION(0x0, "gpio_in"),
		  SUNXI_FUNCTION(0x1, "gpio_out"),
		  SUNXI_FUNCTION(0x2, "lcd1"),		/* D20 */
		  SUNXI_FUNCTION(0x3, "emac0"),		/* ERXDV */
		  SUNXI_FUNCTION(0x4, "can0"),		/* TX */
		  SUNXI_FUNCTION(0x7, "csi1"),		/* D20 */
		  SUNXI_FUNCTION_IRQ_BANK(0x6, 0, 20)),
	SUNXI_PIN(SUNXI_PINCTRL_PIN(H, 21),
		  SUNXI_FUNCTION(0x0, "gpio_in"),
		  SUNXI_FUNCTION(0x1, "gpio_out"),
		  SUNXI_FUNCTION(0x2, "lcd1"),		/* D21 */
		  SUNXI_FUNCTION(0x3, "emac0"),		/* EMDC */
		  SUNXI_FUNCTION(0x4, "can1"),		/* RX */
		  SUNXI_FUNCTION(0x7, "csi1"),		/* D21 */
		  SUNXI_FUNCTION_IRQ_BANK(0x6, 0, 21)),
	SUNXI_PIN(SUNXI_PINCTRL_PIN(H, 22),
		  SUNXI_FUNCTION(0x0, "gpio_in"),
		  SUNXI_FUNCTION(0x1, "gpio_out"),
		  SUNXI_FUNCTION(0x2, "lcd1"),		/* D22 */
		  SUNXI_FUNCTION(0x3, "emac0"),		/* EMDIO */
		  SUNXI_FUNCTION(0x4, "kp0"),		/* OUT2 */
		  SUNXI_FUNCTION(0x5, "sdc1"),		/* CMD */
		  SUNXI_FUNCTION(0x7, "csi1")),		/* D22 */
	SUNXI_PIN(SUNXI_PINCTRL_PIN(H, 23),
		  SUNXI_FUNCTION(0x0, "gpio_in"),
		  SUNXI_FUNCTION(0x1, "gpio_out"),
		  SUNXI_FUNCTION(0x2, "lcd1"),		/* D23 */
		  SUNXI_FUNCTION(0x3, "emac0"),		/* ETXEN */
		  SUNXI_FUNCTION(0x4, "kp0"),		/* OUT3 */
		  SUNXI_FUNCTION(0x5, "sdc1"),		/* CLK */
		  SUNXI_FUNCTION(0x7, "csi1")),		/* D23 */
	SUNXI_PIN(SUNXI_PINCTRL_PIN(H, 24),
		  SUNXI_FUNCTION(0x0, "gpio_in"),
		  SUNXI_FUNCTION(0x1, "gpio_out"),
		  SUNXI_FUNCTION(0x2, "lcd1"),		/* CLK */
		  SUNXI_FUNCTION(0x3, "emac0"),		/* ETXCK */
		  SUNXI_FUNCTION(0x4, "kp0"),		/* OUT4 */
		  SUNXI_FUNCTION(0x5, "sdc1"),		/* D0 */
		  SUNXI_FUNCTION(0x7, "csi1")),		/* PCLK */
	SUNXI_PIN(SUNXI_PINCTRL_PIN(H, 25),
		  SUNXI_FUNCTION(0x0, "gpio_in"),
		  SUNXI_FUNCTION(0x1, "gpio_out"),
		  SUNXI_FUNCTION(0x2, "lcd1"),		/* DE */
		  SUNXI_FUNCTION(0x3, "emac0"),		/* ECRS */
		  SUNXI_FUNCTION(0x4, "kp0"),		/* OUT5 */
		  SUNXI_FUNCTION(0x5, "sdc1"),		/* D1 */
		  SUNXI_FUNCTION(0x7, "csi1")),		/* FIELD */
	SUNXI_PIN(SUNXI_PINCTRL_PIN(H, 26),
		  SUNXI_FUNCTION(0x0, "gpio_in"),
		  SUNXI_FUNCTION(0x1, "gpio_out"),
		  SUNXI_FUNCTION(0x2, "lcd1"),		/* HSYNC */
		  SUNXI_FUNCTION(0x3, "emac0"),		/* ECOL */
		  SUNXI_FUNCTION(0x4, "kp0"),		/* OUT6 */
		  SUNXI_FUNCTION(0x5, "sdc1"),		/* D2 */
		  SUNXI_FUNCTION(0x7, "csi1")),		/* HSYNC */
	SUNXI_PIN(SUNXI_PINCTRL_PIN(H, 27),
		  SUNXI_FUNCTION(0x0, "gpio_in"),
		  SUNXI_FUNCTION(0x1, "gpio_out"),
		  SUNXI_FUNCTION(0x2, "lcd1"),		/* VSYNC */
		  SUNXI_FUNCTION(0x3, "emac0"),		/* ETXERR */
		  SUNXI_FUNCTION(0x4, "kp0"),		/* OUT7 */
		  SUNXI_FUNCTION(0x5, "sdc1"),		/* D3 */
		  SUNXI_FUNCTION(0x7, "csi1")),		/* VSYNC */

	/* Hole */
	SUNXI_PIN(SUNXI_PINCTRL_PIN(I, 0),
		  SUNXI_FUNCTION(0x0, "gpio_in"),
		  SUNXI_FUNCTION(0x1, "gpio_out"),
		  SUNXI_FUNCTION(0x3, "twi3"),		/* SCK */
		  SUNXI_FUNCTION(0x7, "io_disabled")),
	SUNXI_PIN(SUNXI_PINCTRL_PIN(I, 1),
		  SUNXI_FUNCTION(0x0, "gpio_in"),
		  SUNXI_FUNCTION(0x1, "gpio_out"),
		  SUNXI_FUNCTION(0x3, "twi3"),		/* SDA */
		  SUNXI_FUNCTION(0x7, "io_disabled")),
	SUNXI_PIN(SUNXI_PINCTRL_PIN(I, 2),
		  SUNXI_FUNCTION(0x0, "gpio_in"),
		  SUNXI_FUNCTION(0x1, "gpio_out"),
		  SUNXI_FUNCTION(0x3, "twi4"),		/* SCK */
		  SUNXI_FUNCTION(0x7, "io_disabled")),
	SUNXI_PIN(SUNXI_PINCTRL_PIN(I, 3),
		  SUNXI_FUNCTION(0x0, "gpio_in"),
		  SUNXI_FUNCTION(0x1, "gpio_out"),
		  SUNXI_FUNCTION(0x2, "pwm1"),		/* PWM1 */
		  SUNXI_FUNCTION(0x3, "twi4"),		/* SDA */
		  SUNXI_FUNCTION(0x7, "io_disabled")),
	SUNXI_PIN(SUNXI_PINCTRL_PIN(I, 4),
		  SUNXI_FUNCTION(0x0, "gpio_in"),
		  SUNXI_FUNCTION(0x1, "gpio_out"),
		  SUNXI_FUNCTION(0x2, "sdc3"),		/* CMD */
		  SUNXI_FUNCTION(0x7, "io_disabled")),
	SUNXI_PIN(SUNXI_PINCTRL_PIN(I, 5),
		  SUNXI_FUNCTION(0x0, "gpio_in"),
		  SUNXI_FUNCTION(0x1, "gpio_out"),
		  SUNXI_FUNCTION(0x2, "sdc3"),		/* CLK */
		  SUNXI_FUNCTION(0x7, "io_disabled")),
	SUNXI_PIN(SUNXI_PINCTRL_PIN(I, 6),
		  SUNXI_FUNCTION(0x0, "gpio_in"),
		  SUNXI_FUNCTION(0x1, "gpio_out"),
		  SUNXI_FUNCTION(0x2, "sdc3"),		/* D0 */
		  SUNXI_FUNCTION(0x7, "io_disabled")),
	SUNXI_PIN(SUNXI_PINCTRL_PIN(I, 7),
		  SUNXI_FUNCTION(0x0, "gpio_in"),
		  SUNXI_FUNCTION(0x1, "gpio_out"),
		  SUNXI_FUNCTION(0x2, "sdc3"),		/* D1 */
		  SUNXI_FUNCTION(0x7, "io_disabled")),
	SUNXI_PIN(SUNXI_PINCTRL_PIN(I, 8),
		  SUNXI_FUNCTION(0x0, "gpio_in"),
		  SUNXI_FUNCTION(0x1, "gpio_out"),
		  SUNXI_FUNCTION(0x2, "sdc3"),		/* D2 */
		  SUNXI_FUNCTION(0x7, "io_disabled")),
	SUNXI_PIN(SUNXI_PINCTRL_PIN(I, 9),
		  SUNXI_FUNCTION(0x0, "gpio_in"),
		  SUNXI_FUNCTION(0x1, "gpio_out"),
		  SUNXI_FUNCTION(0x2, "sdc3"),		/* D3 */
		  SUNXI_FUNCTION(0x7, "io_disabled")),
	SUNXI_PIN(SUNXI_PINCTRL_PIN(I, 10),
		  SUNXI_FUNCTION(0x0, "gpio_in"),
		  SUNXI_FUNCTION(0x1, "gpio_out"),
		  SUNXI_FUNCTION(0x2, "spi0"),		/* CS0 */
		  SUNXI_FUNCTION(0x3, "uart5"),		/* TX */
		  SUNXI_FUNCTION(0x7, "io_disabled"),
		  SUNXI_FUNCTION_IRQ_BANK(0x6, 0, 22)),
	SUNXI_PIN(SUNXI_PINCTRL_PIN(I, 11),
		  SUNXI_FUNCTION(0x0, "gpio_in"),
		  SUNXI_FUNCTION(0x1, "gpio_out"),
		  SUNXI_FUNCTION(0x2, "spi0"),		/* CLK */
		  SUNXI_FUNCTION(0x3, "uart5"),		/* RX */
		  SUNXI_FUNCTION(0x7, "io_disabled"),
		  SUNXI_FUNCTION_IRQ_BANK(0x6, 0, 23)),
	SUNXI_PIN(SUNXI_PINCTRL_PIN(I, 12),
		  SUNXI_FUNCTION(0x0, "gpio_in"),
		  SUNXI_FUNCTION(0x1, "gpio_out"),
		  SUNXI_FUNCTION(0x2, "spi0"),		/* MOSI */
		  SUNXI_FUNCTION(0x3, "uart6"),		/* TX */
		  SUNXI_FUNCTION(0x4, "clka"),		/* CLK_OUT_A */
		  SUNXI_FUNCTION(0x7, "io_disabled"),
		  SUNXI_FUNCTION_IRQ_BANK(0x6, 0, 24)),
	SUNXI_PIN(SUNXI_PINCTRL_PIN(I, 13),
		  SUNXI_FUNCTION(0x0, "gpio_in"),
		  SUNXI_FUNCTION(0x1, "gpio_out"),
		  SUNXI_FUNCTION(0x2, "spi0"),		/* MISO */
		  SUNXI_FUNCTION(0x3, "uart6"),		/* RX */
		  SUNXI_FUNCTION(0x4, "clkb"),		/* CLK_OUT_B */
		  SUNXI_FUNCTION(0x7, "io_disabled"),
		  SUNXI_FUNCTION_IRQ_BANK(0x6, 0, 25)),
	SUNXI_PIN(SUNXI_PINCTRL_PIN(I, 14),
		  SUNXI_FUNCTION(0x0, "gpio_in"),
		  SUNXI_FUNCTION(0x1, "gpio_out"),
		  SUNXI_FUNCTION(0x2, "spi0"),		/* CS1 */
		  SUNXI_FUNCTION(0x3, "ps2"),		/* SCK1 */
		  SUNXI_FUNCTION(0x4, "tclk"),		/* TCLKIN0 */
		  SUNXI_FUNCTION(0x7, "io_disabled"),
		  SUNXI_FUNCTION_IRQ_BANK(0x6, 0, 26)),
	SUNXI_PIN(SUNXI_PINCTRL_PIN(I, 15),
		  SUNXI_FUNCTION(0x0, "gpio_in"),
		  SUNXI_FUNCTION(0x1, "gpio_out"),
		  SUNXI_FUNCTION(0x2, "spi1"),		/* CS1 */
		  SUNXI_FUNCTION(0x3, "ps2"),		/* SDA1 */
		  SUNXI_FUNCTION(0x4, "tclk"),		/* TCLKIN1 */
		  SUNXI_FUNCTION(0x7, "io_disabled"),
		  SUNXI_FUNCTION_IRQ_BANK(0x6, 0, 27)),
	SUNXI_PIN(SUNXI_PINCTRL_PIN(I, 16),
		  SUNXI_FUNCTION(0x0, "gpio_in"),
		  SUNXI_FUNCTION(0x1, "gpio_out"),
		  SUNXI_FUNCTION(0x2, "spi1"),		/* CS0 */
		  SUNXI_FUNCTION(0x3, "uart2"),		/* RTS */
		  SUNXI_FUNCTION(0x7, "io_disabled"),
		  SUNXI_FUNCTION_IRQ_BANK(0x6, 0, 28)),
	SUNXI_PIN(SUNXI_PINCTRL_PIN(I, 17),
		  SUNXI_FUNCTION(0x0, "gpio_in"),
		  SUNXI_FUNCTION(0x1, "gpio_out"),
		  SUNXI_FUNCTION(0x2, "spi1"),		/* CLK */
		  SUNXI_FUNCTION(0x3, "uart2"),		/* CTS */
		  SUNXI_FUNCTION(0x7, "io_disabled"),
		  SUNXI_FUNCTION_IRQ_BANK(0x6, 0, 29)),
	SUNXI_PIN(SUNXI_PINCTRL_PIN(I, 18),
		  SUNXI_FUNCTION(0x0, "gpio_in"),
		  SUNXI_FUNCTION(0x1, "gpio_out"),
		  SUNXI_FUNCTION(0x2, "spi1"),		/* MOSI */
		  SUNXI_FUNCTION(0x3, "uart2"),		/* TX */
		  SUNXI_FUNCTION(0x7, "io_disabled"),
		  SUNXI_FUNCTION_IRQ_BANK(0x6, 0, 30)),
	SUNXI_PIN(SUNXI_PINCTRL_PIN(I, 19),
		  SUNXI_FUNCTION(0x0, "gpio_in"),
		  SUNXI_FUNCTION(0x1, "gpio_out"),
		  SUNXI_FUNCTION(0x2, "spi1"),		/* MISO */
		  SUNXI_FUNCTION(0x3, "uart2"),		/* RX */
		  SUNXI_FUNCTION(0x7, "io_disabled"),
		  SUNXI_FUNCTION_IRQ_BANK(0x6, 0, 31)),
	SUNXI_PIN(SUNXI_PINCTRL_PIN(I, 20),
		  SUNXI_FUNCTION(0x0, "gpio_in"),
		  SUNXI_FUNCTION(0x1, "gpio_out"),
		  SUNXI_FUNCTION(0x2, "ps2"),		/* SCK0 */
		  SUNXI_FUNCTION(0x3, "uart7"),		/* TX */
		  SUNXI_FUNCTION(0x4, "hdmi"),		/* HSCL */
		  SUNXI_FUNCTION(0x7, "io_disabled")),
	SUNXI_PIN(SUNXI_PINCTRL_PIN(I, 21),
		  SUNXI_FUNCTION(0x0, "gpio_in"),
		  SUNXI_FUNCTION(0x1, "gpio_out"),
		  SUNXI_FUNCTION(0x2, "ps2"),		/* SDA0 */
		  SUNXI_FUNCTION(0x3, "uart7"),		/* RX */
		  SUNXI_FUNCTION(0x4, "hdmi"),		/* HSDA */
		  SUNXI_FUNCTION(0x7, "io_disabled")),
};
static const struct sunxi_pinctrl_desc sun8iw11p1_pinctrl_data = {
	.pins = sun8iw11p1_pins,
	.npins = ARRAY_SIZE(sun8iw11p1_pins),
	.pin_base = 0,
	.irq_banks = 1,
};

static int sun8iw11p1_pinctrl_probe(struct platform_device *pdev)
{
	return sunxi_pinctrl_init(pdev,
				  &sun8iw11p1_pinctrl_data);
}

static struct of_device_id sun8iw11p1_pinctrl_match[] = {
	{ .compatible = "allwinner,sun8iw11p1-pinctrl", },
	{}
};
MODULE_DEVICE_TABLE(of, sun8iw11p1_pinctrl_match);

static struct platform_driver sun8iw11p1_pinctrl_driver = {
	.probe	= sun8iw11p1_pinctrl_probe,
	.driver	= {
		.name		= "sun8iw11p1-pinctrl",
		.owner		= THIS_MODULE,
		.of_match_table	= sun8iw11p1_pinctrl_match,
	},
};
static int __init sun8iw11p1_pio_init(void)
{
	int ret;
	ret = platform_driver_register(&sun8iw11p1_pinctrl_driver);
	if (IS_ERR_VALUE(ret)) {
		pr_debug("register sun8iw11p1 pio controller failed\n");
		return -EINVAL;
	}
	return 0;
}
postcore_initcall(sun8iw11p1_pio_init);

MODULE_AUTHOR("Jackie Hwang <huangshr@allwinnertech.com>");
MODULE_AUTHOR("Chen-Yu Tsai <wens@csie.org>");
MODULE_AUTHOR("Boris Brezillon <boris.brezillon@free-electrons.com");
MODULE_AUTHOR("Maxime Ripard <maxime.ripard@free-electrons.com");
MODULE_DESCRIPTION("Allwinner sun8iw11p1 PIO pinctrl driver");
MODULE_LICENSE("GPL");
