OLIMEX/DIY-LAPTOP/SOFTWARE/A64-TERES/linux-a64/drivers/input/touchscreen/ft5x/ft5x02_ini_config.h

#ifndef __LINUX_FT5X02_INI_CONFIG_H__
#define __LINUX_FT5X02_INI_CONFIG_H


/*Init param register address*/
/*factory mode register*/
#define FT5x02_REG_TX_NUM				0x03
#define FT5x02_REG_RX_NUM				0x04
#define FT5x02_REG_VOLTAGE				0x05
#define FT5x02_REG_GAIN					0x07
#define FT5X02_REG_SCAN_SELECT		                0x4E
#define FT5x02_REG_TX_ORDER_START		        0x50
#define FT5x02_REG_TX_CAP_START		                0x78
#define FT5x02_REG_TX_OFFSET_START	                0xBF
#define FT5x02_REG_RX_ORDER_START		        0xea
#define FT5x02_REG_RX_CAP_START		                0xA0
#define FT5x02_REG_RX_OFFSET_START	                0xD3
#define FT5X02_REG_START_RX			        0x06
#define FT5X02_REG_ADC_TARGET_HIGH	                0x08
#define FT5X02_REG_ADC_TARGET_LOW	                0x09


#define FT5x02_REG_DEVICE_MODE		                0x00

/*work mode register*/
#define FT5X02_REG_THGROUP				(0x00+0x80)
#define FT5X02_REG_THPEAK 				(0x01+0x80)
#define FT5X02_REG_THCAL 				(0x02+0x80)
#define FT5X02_REG_THWATER 			        (0x03+0x80)
#define FT5X02_REG_THFALSE_TOUCH_PEAK 		        (0x04+0x80)
#define FT5X02_REG_THDIFF				(0x05+0x80)
#define FT5X02_REG_PWMODE_CTRL				(0x06+0x80)
#define FT5X02_REG_TIME_ENTER_MONITOR 		        (0x07+0x80)
#define FT5X02_REG_PERIOD_ACTIVE		        (0x08+0x80)
#define FT5X02_REG_PERIOD_MONITOR 			(0x09+0x80)
#define FT5X02_REG_POINTS_SUPPORTED			(0x0A+0x80)
#define FT5X02_REG_ESD_FILTER_FRAME			(0x11+0x80)
#define FT5x02_REG_RESOLUTION_X_H			(0x18+0x80)
#define FT5x02_REG_RESOLUTION_X_L		        (0x19+0x80)
#define FT5x02_REG_RESOLUTION_Y_H		        (0x1a+0x80)
#define FT5x02_REG_RESOLUTION_Y_L		        (0x1b+0x80)
#define FT5X02_REG_KX_H				        (0x1c+0x80)
#define FT5X02_REG_KX_L				        (0x1d+0x80)
#define FT5X02_REG_KY_H				        0x9e
#define FT5X02_REG_KY_L				        (0x1f+0x80)
#define FT5X02_REG_AUTO_CLB_MODE		        (0x20+0x80)
#define FT5X02_REG_LIB_VERSION_H		        (0x21+0x80)
#define FT5X02_REG_LIB_VERSION_L		        (0x22+0x80)
#define FT5X02_REG_CIPHER_ID			        (0x23+0x80)
#define FT5X02_REG_MODE				        (0x24+0x80)
#define FT5X02_REG_PMODE			        (0x25+0x80)
#define FT5X02_REG_FIRMWARE_ID				(0x26+0x80)
#define FT5X02_REG_STATE			        (0x27+0x80)
#define FT5X02_REG_CUSTOMER_ID				(0x28+0x80) 
#define FT5X02_REG_OTP_PARAM_ID				(0x2A+0x80)
#define FT5X02_REG_STATIC_TH				(0x2b+0x80)
#define FT5X02_REG_DRAW_LINE_TH				0xae
#define FT5X02_REG_FACE_DETECT_MODE			(0x33+0x80)
#define FT5X02_REG_MAX_TOUCH_VALUE_HIGH		        (0x34+0x80)
#define FT5X02_REG_MAX_TOUCH_VALUE_LOW		        (0x35+0x80)
#define FT5X02_REG_MOVSTH_I				(0x36+0x80)
#define FT5X02_REG_MOVSTH_N				(0x37+0x80)
#define FT5X02_REG_DIRECTION				(0x40+0x80)
#define FT5X02_REG_LEMDA_X				(0x41+0x80)
#define FT5X02_REG_LEMDA_Y				(0x42+0x80)
#define FT5X02_REG_FACE_DETECT_STATISTICS_TX_NUM	(0x43+0x80)
#define FT5X02_REG_FACE_DETECT_PRE_VALUE		(0x44+0x80)
#define FT5X02_REG_FACE_DETECT_NUM			(0x45+0x80)
#define FT5X02_REG_FACE_DETECT_LAST_TIME_H	        (0x46+0x80)
#define FT5X02_REG_FACE_DETECT_LAST_TIME_L	        (0x47+0x80)
#define FT5X02_REG_FACE_DETECT_ON		        (0x48+0x80)
#define FT5X02_REG_FACE_DETECT_OFF			(0x49+0x80)
#define FT5X02_REG_BIGAREA_PEAK_VALUE_MIN	        (0x4a+0x80)
#define FT5X02_REG_BIGAREA_DIFF_VALUE_OVER_NUM		(0x4b+0x80)	
#define FT5X02_REG_BIGAREA_POINT_AUTO_CLEAR_TIME_H	(0x4c+0x80)
#define FT5X02_REG_BIGAREA_POINT_AUTO_CLEAR_TIME_L	(0x4d+0x80)
#define FT5X02_REG_DIFFDATA_HADDLE_VALUE                0xce//(0x4e+0x80)
#define FT5X02_REG_ABNORMAL_DIFF_VALUE		        (0x4f+0x80)
#define FT5X02_REG_ABNORMAL_DIFF_NUM			(0x50+0x80)
#define FT5X02_REG_ABNORMAL_DIFF_LAST_FRAME	        (0x51+0x80)
#define FT5X02_REG_MID_SPEED_TH				(0x2C+0x80)
#define FT5X02_REG_HIGH_SPEED_TH			(0x2D+0x80)
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
